bluepylons/Open-Switch-Curve-Meter/Pics/Gen-2-front-no-keycap.JPG

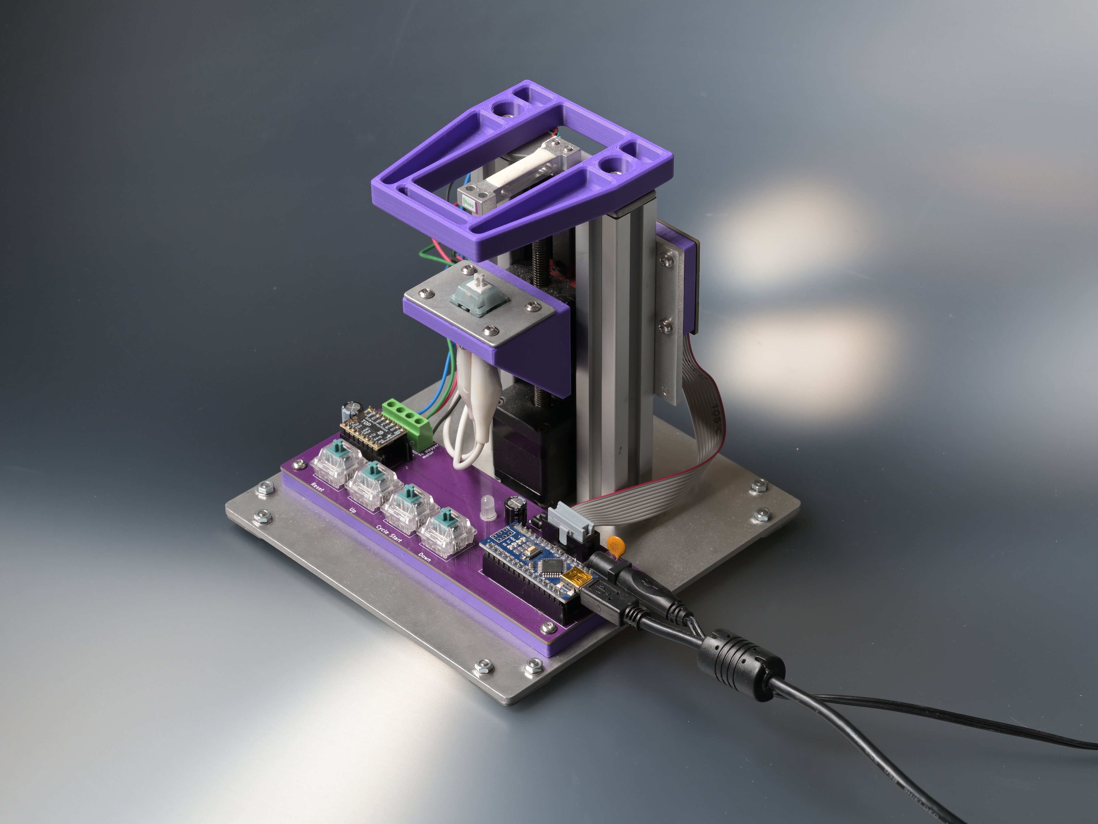
Pics/Gen-2-front-no-keycap.JPG
