bluepylons/Open-Switch-Curve-Meter/Pics/Gen-2.JPG

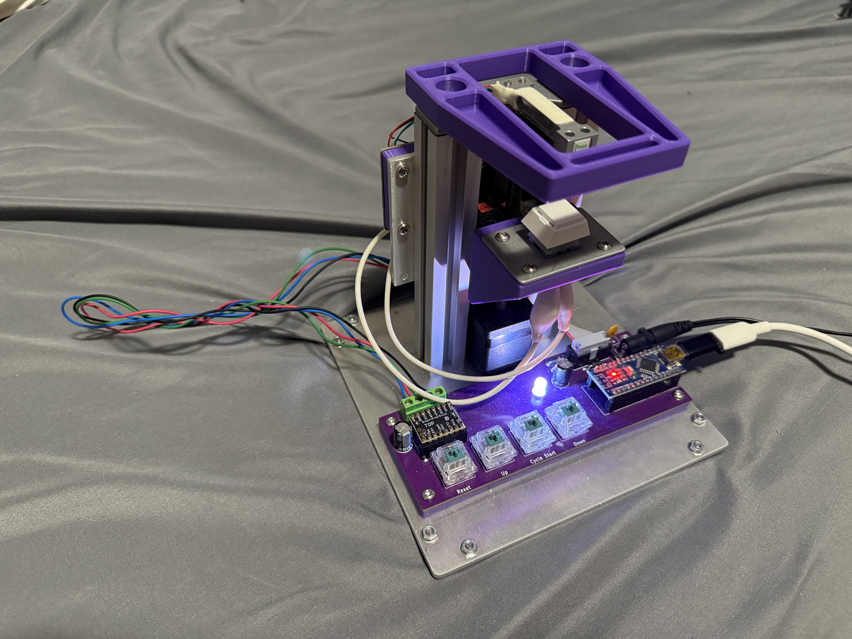
Pics/Gen-2.JPG
