bluepylons/Open-Switch-Curve-Meter/Pics/IMG_0680.JPG

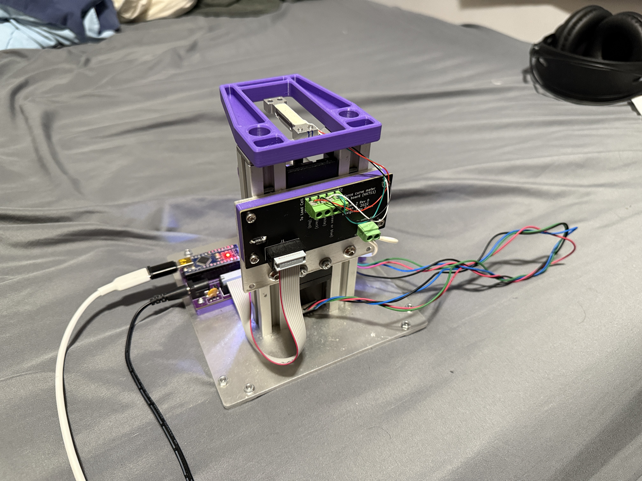
Pics/IMG_0680.JPG
