bluepylons/Open-Switch-Curve-Meter/Pics/Prototype-1-vertical.jpg

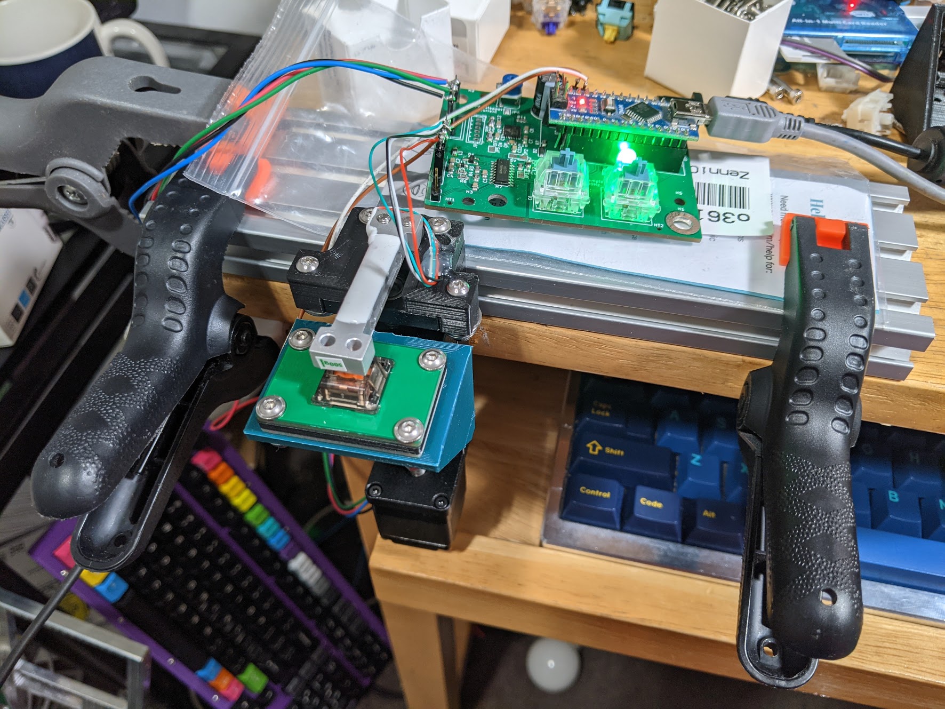
Pics/Prototype-1-vertical.jpg
