bluepylons/Open-Switch-Curve-Meter/Pics/Prototype-1.jpg

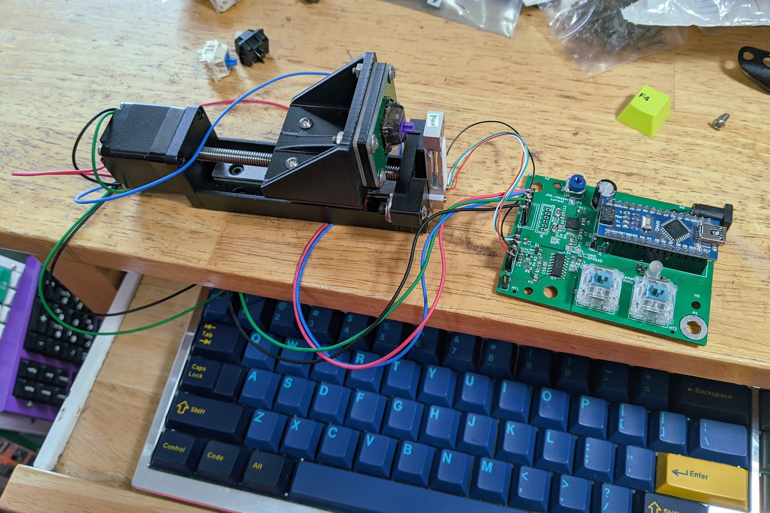
Pics/Prototype-1.jpg
