bluepylons/Open-Switch-Curve-Meter/Gen 2 Design/Mechanical files/Laser cut/Load-cell-mounting-plate.stp

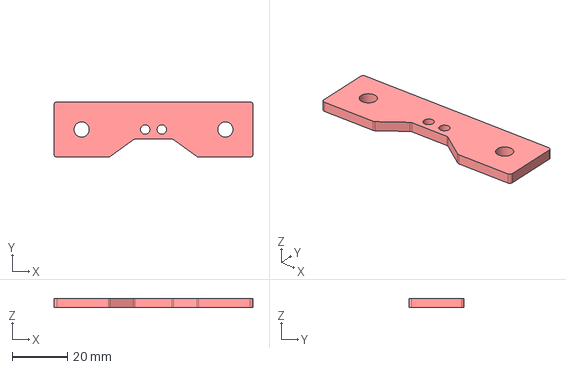
[picture p144: CAD file, 2026-01-06]
Gen 2 Design/Mechanical files/Laser cut/Load-cell-mounting-plate.stp
72.0 x 20.0 x 3.17 mm
