bluepylons/Open-Switch-Curve-Meter/CAD (Atom3D)/STLs/Switch-mounting-bracket.stl

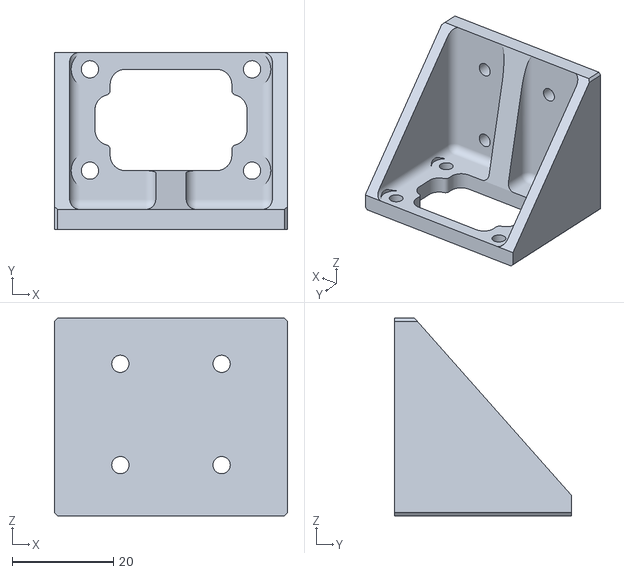
[picture p145: CAD file, 2021-06-18]
CAD (Atom3D)/STLs/Switch-mounting-bracket.stl
46.0 x 35.0 x 39.0
