bluepylons/Open-Switch-Curve-Meter/Gen 2 Design/Mechanical files/Laser cut/Baseplate-stand.stp

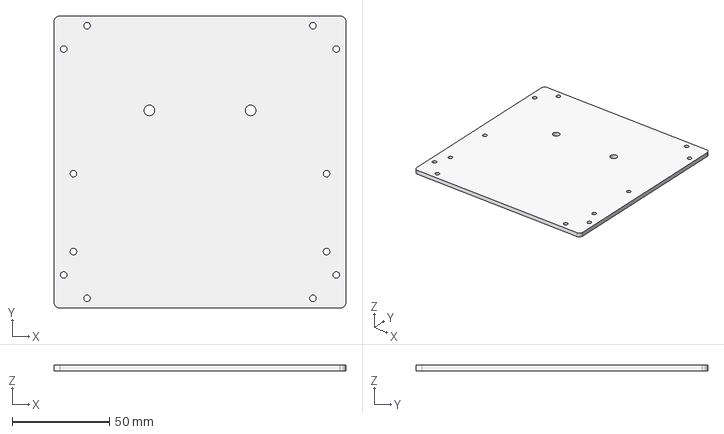
[picture p146: CAD file, 2026-01-06]
Gen 2 Design/Mechanical files/Laser cut/Baseplate-stand.stp
150.0 x 150.0 x 3.17 mm
