bluepylons/Open-Switch-Curve-Meter/Gen 2 Design/Mechanical files/Atom3D CAD files/M3-hex-nut-DIN-934.step

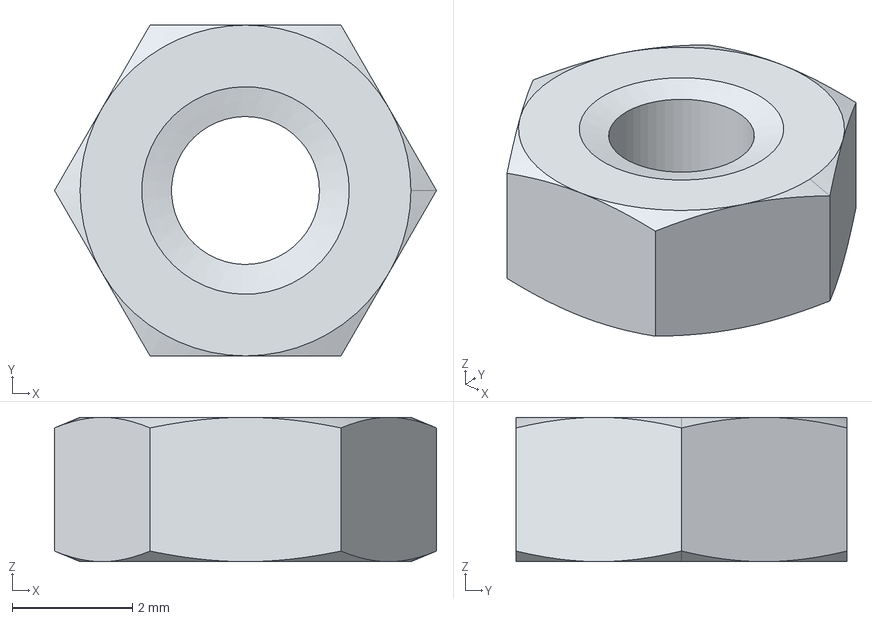
[picture p147: CAD file, 2026-01-05]
Gen 2 Design/Mechanical files/Atom3D CAD files/M3-hex-nut-DIN-934.step
6.35 x 5.50 x 2.40 mm
