bluepylons/Open-Switch-Curve-Meter/Force curves/Okay-I'm-Just-Going-to-Calibrate-Every-Day-Now/Feker-Smoky-Tactile-Stem-In-T1-Housing.ods

Raw data |  |  |  | Corrected Downstroke |  | Corrected Upstroke
X (microns) | Force (gf) | Actuated? | Tared | X (mm) | Force (gf) | X (mm) | Force (gf)
0 | -0.03 | 0 |  | 0 | 0.51 | 2.785 | 91.39
5 | -0.02 | 0 |  | 0.005 | 3.07 | 2.78 | 75.15
10 | -0.02 | 0 |  | 0.01 | 16.92 | 2.775 | 67.36
15 | -0.06 | 0 |  | 0.015 | 23.72 | 2.77 | 54.02
20 | -0.02 | 0 |  | 0.02 | 25.77 | 2.765 | 52.09
25 | -0.02 | 0 |  | 0.025 | 25.64 | 2.76 | 51.23
30 | -0.02 | 0 |  | 0.03 | 25.82 | 2.755 | 50.56
35 | -0.03 | 0 |  | 0.035 | 26.11 | 2.75 | 50.32
40 | -0.01 | 0 |  | 0.04 | 28.4 | 2.745 | 49.74
45 | -0.01 | 0 |  | 0.045 | 30.32 | 2.74 | 49.52
50 | 0 | 0 |  | 0.05 | 32.86 | 2.735 | 48.82
55 | 0 | 0 |  | 0.055 | 33.33 | 2.73 | 48.6
60 | -0.02 | 0 |  | 0.06 | 33.56 | 2.725 | 48.03
65 | -0.01 | 0 |  | 0.065 | 33.83 | 2.72 | 47.85
70 | 0 | 0 |  | 0.07 | 34.03 | 2.715 | 47.09
75 | -0.01 | 0 |  | 0.075 | 34.58 | 2.71 | 46.87
80 | 0 | 0 |  | 0.08 | 34.84 | 2.705 | 46.27
85 | -0.02 | 0 |  | 0.085 | 35.52 | 2.7 | 46.1
90 | 0 | 0 |  | 0.09 | 35.88 | 2.695 | 45.35
95 | -0.01 | 0 |  | 0.095 | 36.65 | 2.69 | 45.08
100 | 0.01 | 0 |  | 0.1 | 36.83 | 2.685 | 44.39
105 | 0.03 | 0 |  | 0.105 | 37.09 | 2.68 | 44.19
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
