bluepylons/Open-Switch-Curve-Meter/Force curves/Okay-I'm-Just-Going-to-Calibrate-Every-Day-Now/NK-Blueberry-stem-in-Tecsee-Lychee.ods

Raw data |  |  |  | Corrected Downstroke |  | Corrected Upstroke
X (microns) | Force (gf) | Actuated? | Tared | X (mm) | Force (gf) | X (mm) | Force (gf)
0 | -0.05 | 0 | 0 | 0 | 0.42 | 3.72 | 67.65
5 | -0.04 | 0 | 0.01 | 0.005 | 9.39 | 3.715 | 67.37
10 | -0.03 | 0 | 0.02 | 0.01 | 16.71 | 3.71 | 67.28
15 | -0.05 | 0 | 0 | 0.015 | 31.33 | 3.705 | 67.06
20 | -0.02 | 0 | 0.03 | 0.02 | 38.25 | 3.7 | 66.91
25 | -0.06 | 0 | -0.01 | 0.025 | 45.42 | 3.695 | 66.81
30 | -0.06 | 0 | -0.01 | 0.03 | 47.04 | 3.69 | 66.65
35 | -0.03 | 0 | 0.02 | 0.035 | 49.03 | 3.685 | 66.52
40 | -0.04 | 0 | 0.01 | 0.04 | 49.46 | 3.68 | 66.21
45 | -0.05 | 0 | 0 | 0.045 | 49.41 | 3.675 | 66.19
50 | -0.04 | 0 | 0.01 | 0.05 | 49.43 | 3.67 | 65.96
55 | -0.05 | 0 | 0 | 0.055 | 49.05 | 3.665 | 65.89
60 | -0.03 | 0 | 0.02 | 0.06 | 48.96 | 3.66 | 65.76
65 | -0.03 | 0 | 0.02 | 0.065 | 48.92 | 3.655 | 65.71
70 | -0.03 | 0 | 0.02 | 0.07 | 49.04 | 3.65 | 65.51
75 | -0.05 | 0 | 0 | 0.075 | 49.07 | 3.645 | 65.44
80 | -0.07 | 0 | -0.02 | 0.08 | 48.9 | 3.64 | 65.32
85 | -0.06 | 0 | -0.01 | 0.085 | 48.72 | 3.635 | 65.23
90 | 0 | 0 | 0.05 | 0.09 | 48.79 | 3.63 | 65
95 | -0.01 | 0 | 0.04 | 0.095 | 48.72 | 3.625 | 64.91
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
