bluepylons/Open-Switch-Curve-Meter/Force curves/Okay-I'm-Just-Going-to-Calibrate-Every-Day-Now/Durock-Shrimp.ods

Raw data |  |  |  | Corrected Downstroke |  | Corrected Upstroke
X (microns) | Force (gf) | Actuated? | Tared | X (mm) | Force (gf) | X (mm) | Force (gf)
0 | -0.02 | 0 | 0 | 0 | 3.27 | 3.37 | 108.52
5 | -0.03 | 0 | -0.01 | 0.005 | 7.87 | 3.365 | 104.4
10 | -0.01 | 0 | 0.01 | 0.01 | 17.7 | 3.36 | 97.14
15 | -0.03 | 0 | -0.01 | 0.015 | 22.87 | 3.355 | 93.87
20 | -0.04 | 0 | -0.02 | 0.02 | 29.94 | 3.35 | 88.1
25 | -0.02 | 0 | 0 | 0.025 | 31.75 | 3.345 | 85.55
30 | -0.03 | 0 | -0.01 | 0.03 | 35.33 | 3.34 | 81.15
35 | -0.03 | 0 | -0.01 | 0.035 | 37.24 | 3.335 | 77.59
40 | -0.02 | 0 | 0 | 0.04 | 41.13 | 3.33 | 75.82
45 | -0.01 | 0 | 0.01 | 0.045 | 44.83 | 3.325 | 72.72
50 | 0 | 0 | 0.02 | 0.05 | 46.64 | 3.32 | 71.4
55 | 0.01 | 0 | 0.03 | 0.055 | 49.84 | 3.315 | 69.27
60 | -0.04 | 0 | -0.02 | 0.06 | 51.35 | 3.31 | 68.26
65 | -0.02 | 0 | 0 | 0.065 | 53.95 | 3.305 | 66.72
70 | -0.01 | 0 | 0.01 | 0.07 | 55.09 | 3.3 | 65.96
75 | -0.02 | 0 | 0 | 0.075 | 56.88 | 3.295 | 64.92
80 | -0.05 | 0 | -0.03 | 0.08 | 57.79 | 3.29 | 64.85
85 | 0.02 | 0 | 0.04 | 0.085 | 59.82 | 3.285 | 64.71
90 | 0.02 | 0 | 0.04 | 0.09 | 60.61 | 3.28 | 64.5
95 | -0.03 | 0 | -0.01 | 0.095 | 61.62 | 3.275 | 64.06
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
