bluepylons/Open-Switch-Curve-Meter/Force curves/Okay-I'm-Just-Going-to-Calibrate-Every-Day-Now/Gateron-Silver-Blizzard.ods

Raw data |  |  |  | Corrected Downstroke |  | Corrected Upstroke
X (microns) | Force (gf) | Actuated? | Tared | X (mm) | Force (gf) | X (mm) | Force (gf)
0 | 0.05 | 0 | 0 | 0 | 7 | 3.405 | 116.66
5 | 0.03 | 0 | -0.02 | 0.005 | 20.95 | 3.4 | 106.08
10 | 0.07 | 0 | 0.02 | 0.01 | 28.46 | 3.395 | 95.47
15 | 0.07 | 0 | 0.02 | 0.015 | 34.38 | 3.39 | 90.1
20 | 0.07 | 0 | 0.02 | 0.02 | 36.03 | 3.385 | 80.31
25 | 0.06 | 0 | 0.01 | 0.025 | 39.83 | 3.38 | 75.6
30 | 0.06 | 0 | 0.01 | 0.03 | 41.95 | 3.375 | 67.47
35 | 0.1 | 0 | 0.05 | 0.035 | 43.49 | 3.37 | 63.79
40 | 0.09 | 0 | 0.04 | 0.04 | 43.68 | 3.365 | 60.44
45 | 0.06 | 0 | 0.01 | 0.045 | 43.7 | 3.36 | 60.06
50 | 0.06 | 0 | 0.01 | 0.05 | 43.78 | 3.355 | 59.96
55 | 0.07 | 0 | 0.02 | 0.055 | 43.83 | 3.35 | 59.39
60 | 0.08 | 0 | 0.03 | 0.06 | 43.97 | 3.345 | 59
65 | 0.08 | 0 | 0.03 | 0.065 | 44.25 | 3.34 | 58.92
70 | 0.05 | 0 | 0 | 0.07 | 44.45 | 3.335 | 58.85
75 | 0.07 | 0 | 0.02 | 0.075 | 44.85 | 3.33 | 58.87
80 | 0.07 | 0 | 0.02 | 0.08 | 45.16 | 3.325 | 58.83
85 | 0.05 | 0 | 0 | 0.085 | 45.56 | 3.31999999999999 | 58.83
90 | 0.06 | 0 | 0.01 | 0.09 | 45.76 | 3.31499999999999 | 58.77
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
