bluepylons/Open-Switch-Curve-Meter/Force curves/Okay-I'm-Just-Going-to-Calibrate-Every-Day-Now/Gateron-Slate.ods

Raw data |  |  |  | Corrected Downstroke |  | Corrected Upstroke
X (microns) | Force (gf) | Actuated? | Tared | X (mm) | Force (gf) | X (mm) | Force (gf)
0 | 0.03 | 0 |  | 0 | 0.48 | 3.29 | 121
5 | 0.03 | 0 |  | 0.005 | 3.63 | 3.285 | 111.89
10 | 0.03 | 0 |  | 0.01 | 8.76 | 3.28 | 94.68
15 | 0.03 | 0 |  | 0.015 | 10.79 | 3.275 | 85.71
20 | 0.02 | 0 |  | 0.02 | 13.8 | 3.27 | 69.55
25 | 0 | 0 |  | 0.025 | 15.12 | 3.265 | 62.01
30 | 0 | 0 |  | 0.03 | 16.96 | 3.26 | 52.27
35 | 0 | 0 |  | 0.035 | 17.58 | 3.255 | 51.31
40 | -0.01 | 0 |  | 0.04 | 17.63 | 3.25 | 51.12
45 | 0.01 | 0 |  | 0.045 | 17.48 | 3.245 | 51.04
50 | -0.02 | 0 |  | 0.05 | 17.34 | 3.24 | 51.08
55 | -0.02 | 0 |  | 0.055 | 17.4 | 3.235 | 51.02
60 | -0.01 | 0 |  | 0.06 | 17.5 | 3.23 | 51.11
65 | -0.02 | 0 |  | 0.065 | 17.58 | 3.225 | 51.02
70 | -0.04 | 0 |  | 0.07 | 17.74 | 3.22 | 50.96
75 | -0.02 | 0 |  | 0.075 | 23.82 | 3.215 | 50.72
80 | -0.05 | 0 |  | 0.08 | 28.02 | 3.21 | 50.77
85 | -0.04 | 0 |  | 0.085 | 30.29 | 3.205 | 50.66
90 | -0.06 | 0 |  | 0.09 | 30.11 | 3.2 | 50.66
95 | -0.03 | 0 |  | 0.095 | 30.1 | 3.195 | 50.61
100 | -0.06 | 0 |  | 0.1 | 30.07 | 3.19 | 50.59
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
