bluepylons/Open-Switch-Curve-Meter/Force curves/Okay-I'm-Just-Going-to-Calibrate-Every-Day-Now/KTT-Kang-White.ods

Raw data |  |  |  | Corrected Downstroke |  | Corrected Upstroke
X (microns) | Force (gf) | Actuated? | Tared | X (mm) | Force (gf) | X (mm) | Force (gf)
0 | 0.2 | 0 | -0.01 | 0 | 0.37 | 3.615 | 123.38
5 | 0.18 | 0 | -0.03 | 0.005 | 0.93 | 3.61 | 117.54
10 | 0.19 | 0 | -0.02 | 0.01 | 6.01 | 3.605 | 104.13
15 | 0.17 | 0 | -0.04 | 0.015 | 10.67 | 3.6 | 97.31
20 | 0.18 | 0 | -0.03 | 0.02 | 19.53 | 3.595 | 83.08
25 | 0.17 | 0 | -0.04 | 0.025 | 22.4 | 3.59 | 76.4
30 | 0.15 | 0 | -0.06 | 0.03 | 26.92 | 3.585 | 63.38
35 | 0.15 | 0 | -0.06 | 0.035 | 27.87 | 3.58 | 58.81
40 | 0.16 | 0 | -0.05 | 0.04 | 28.86 | 3.575 | 55.71
45 | 0.17 | 0 | -0.04 | 0.045 | 28.75 | 3.57 | 55.43
50 | 0.2 | 0 | -0.01 | 0.05 | 28.42 | 3.565 | 55.35
55 | 0.21 | 0 | 0 | 0.055 | 28.39 | 3.56 | 55.22
60 | 0.18 | 0 | -0.03 | 0.06 | 28.32 | 3.555 | 55.17
65 | 0.2 | 0 | -0.01 | 0.065 | 28.28 | 3.55 | 55.06
70 | 0.21 | 0 | 0 | 0.07 | 28.13 | 3.545 | 54.98
75 | 0.2 | 0 | -0.01 | 0.075 | 28.07 | 3.54 | 54.87
80 | 0.2 | 0 | -0.01 | 0.08 | 28.02 | 3.535 | 54.81
85 | 0.23 | 0 | 0.02 | 0.085 | 27.96 | 3.52999999999999 | 54.68
90 | 0.17 | 0 | -0.04 | 0.09 | 28 | 3.52499999999999 | 54.62
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
