bluepylons/Open-Switch-Curve-Meter/Force curves/Okay-I'm-Just-Going-to-Calibrate-Every-Day-Now/Tecsee-Lychee.ods

Raw data |  |  |  | Corrected Downstroke |  | Corrected Upstroke
X (microns) | Force (gf) | Actuated? | Tared | X (mm) | Force (gf) | X (mm) | Force (gf)
0 | 0.16 | 0 | 0 | 0 | 0.09 | 3.88 | 80.56
5 | 0.16 | 0 | 0 | 0.005 | 0.5 | 3.875 | 75.22
10 | 0.16 | 0 | 0 | 0.01 | 10.38 | 3.87 | 72.97
15 | 0.16 | 0 | 0 | 0.015 | 16.93 | 3.865 | 70.99
20 | 0.18 | 0 | 0.02 | 0.02 | 30.21 | 3.86 | 70.44
25 | 0.19 | 0 | 0.03 | 0.025 | 36.76 | 3.855 | 69.81
30 | 0.18 | 0 | 0.02 | 0.03 | 47.93 | 3.85 | 69.46
35 | 0.18 | 0 | 0.02 | 0.035 | 52.2 | 3.845 | 68.75
40 | 0.18 | 0 | 0.02 | 0.04 | 55.65 | 3.84 | 68.3
45 | 0.18 | 0 | 0.02 | 0.045 | 55.68 | 3.835 | 67.7
50 | 0.19 | 0 | 0.03 | 0.05 | 55.62 | 3.83 | 67.52
55 | 0.17 | 0 | 0.01 | 0.055 | 55.86 | 3.825 | 67.38
60 | 0.17 | 0 | 0.01 | 0.06 | 56.45 | 3.82 | 67.32
65 | 0.19 | 0 | 0.03 | 0.065 | 56.6 | 3.815 | 67.25
70 | 0.17 | 0 | 0.01 | 0.07 | 56.8 | 3.81 | 67.18
75 | 0.18 | 0 | 0.02 | 0.075 | 56.74 | 3.805 | 67.11
80 | 0.21 | 0 | 0.05 | 0.08 | 56.82 | 3.8 | 67.1
85 | 0.19 | 0 | 0.03 | 0.085 | 56.94 | 3.795 | 67.03
90 | 0.17 | 0 | 0.01 | 0.09 | 57.11 | 3.79 | 66.96
95 | 0.21 | 0 | 0.05 | 0.095 | 57.2 | 3.785 | 66.93
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
