bluepylons/Open-Switch-Curve-Meter/Force curves/Okay-I'm-Just-Going-to-Calibrate-Every-Day-Now/Tecsee-Ruby-V1.ods

Raw data |  |  |  | Corrected Downstroke |  | Corrected Upstroke
X (microns) | Force (gf) | Actuated? | Tared | X (mm) | Force (gf) | X (mm) | Force (gf)
0 | 0 | 0 |  | 0 | 0.15 | 3.415 | 71.68
5 | -0.01 | 0 |  | 0.005 | 7.84 | 3.41 | 71.55
10 | 0 | 0 |  | 0.01 | 15.3 | 3.405 | 71.46
15 | -0.02 | 0 |  | 0.015 | 26.64 | 3.4 | 71.39
20 | 0.01 | 0 |  | 0.02 | 28.04 | 3.395 | 71.31
25 | -0.01 | 0 |  | 0.025 | 29.13 | 3.39 | 71.19
30 | -0.01 | 0 |  | 0.03 | 29.69 | 3.385 | 71.08
35 | -0.02 | 0 |  | 0.035 | 30.95 | 3.38 | 71.01
40 | -0.04 | 0 |  | 0.04 | 31.38 | 3.375 | 70.97
45 | -0.05 | 0 |  | 0.045 | 32.06 | 3.37 | 70.89
50 | -0.02 | 0 |  | 0.05 | 32.1 | 3.365 | 70.73
55 | -0.04 | 0 |  | 0.055 | 31.86 | 3.36 | 70.72
60 | -0.04 | 0 |  | 0.06 | 31.78 | 3.355 | 70.66
65 | -0.03 | 0 |  | 0.065 | 31.7 | 3.35 | 70.62
70 | -0.02 | 0 |  | 0.07 | 31.69 | 3.345 | 70.49
75 | -0.07 | 0 |  | 0.075 | 31.49 | 3.34 | 70.42
80 | -0.05 | 0 |  | 0.08 | 31.5 | 3.335 | 70.38
85 | -0.06 | 0 |  | 0.085 | 31.43 | 3.33 | 70.33
90 | -0.05 | 0 |  | 0.09 | 31.17 | 3.325 | 70.23
95 | -0.08 | 0 |  | 0.095 | 31.07 | 3.32 | 70.18
100 | -0.07 | 0 |  | 0.1 | 31.08 | 3.315 | 70.09
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
