bluepylons/Open-Switch-Curve-Meter/Force curves/Okay-I'm-Just-Going-to-Calibrate-Every-Day-Now/Tecsee-Sapphire-V1.ods

Raw data |  |  |  | Corrected Downstroke |  | Corrected Upstroke
X (microns) | Force (gf) | Actuated? | Tared | X (mm) | Force (gf) | X (mm) | Force (gf)
0 | 0.09 | 0 | 0 | 0 | 0.23 | 3.255 | 92.88
5 | 0.09 | 0 | 0 | 0.005 | 8.58 | 3.25 | 86.68
10 | 0.09 | 0 | 0 | 0.01 | 15.42 | 3.245 | 74.55
15 | 0.07 | 0 | -0.02 | 0.015 | 27.36 | 3.24 | 67.64
20 | 0.02 | 0 | -0.07 | 0.02 | 33.07 | 3.235 | 67.29
25 | 0.06 | 0 | -0.03 | 0.025 | 40.42 | 3.23 | 67.05
30 | 0.04 | 0 | -0.05 | 0.03 | 41.7 | 3.225 | 66.92
35 | 0.06 | 0 | -0.03 | 0.035 | 42.23 | 3.22 | 66.75
40 | 0.04 | 0 | -0.05 | 0.04 | 42.4 | 3.215 | 66.79
45 | 0.06 | 0 | -0.03 | 0.045 | 42.26 | 3.21 | 66.64
50 | 0.03 | 0 | -0.06 | 0.05 | 42.3 | 3.205 | 66.54
55 | 0.05 | 0 | -0.04 | 0.055 | 42.14 | 3.2 | 66.49
60 | 0.05 | 0 | -0.04 | 0.06 | 41.88 | 3.195 | 66.4
65 | 0.07 | 0 | -0.02 | 0.065 | 41.19 | 3.19 | 66.34
70 | 0.04 | 0 | -0.05 | 0.07 | 40.39 | 3.185 | 66.2
75 | 0.07 | 0 | -0.02 | 0.075 | 40.14 | 3.18 | 66.24
80 | 0.06 | 0 | -0.03 | 0.08 | 40.63 | 3.175 | 66.14
85 | 0.07 | 0 | -0.02 | 0.085 | 40.9 | 3.17 | 66.01
90 | 0.07 | 0 | -0.02 | 0.09 | 41.75 | 3.165 | 66.06
95 | 0.09 | 0 | 0 | 0.095 | 42.38 | 3.16 | 65.96
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
