bluepylons/Open-Switch-Curve-Meter/Force curves/Okay-I'm-Just-Going-to-Calibrate-Every-Day-Now/TTC-Golden-Blue.ods

Raw data |  |  |  | Corrected Downstroke |  | Corrected Upstroke
X (microns) | Force (gf) | Actuated? | Tared | X (mm) | Force (gf) | X (mm) | Force (gf)
0 | 0.02 | 0 |  | 0 | 0.22 | 3.535 | 109.77
5 | 0.03 | 0 |  | 0.005 | 0.94 | 3.53 | 108.25
10 | 0.04 | 0 |  | 0.01 | 2.49 | 3.525 | 105.28
15 | -0.01 | 0 |  | 0.015 | 3.18 | 3.52 | 103.77
20 | -0.01 | 0 |  | 0.02 | 4.56 | 3.515 | 100.98
25 | 0.01 | 0 |  | 0.025 | 5.87 | 3.51 | 99.6
30 | 0.22 | 0 |  | 0.03 | 6.56 | 3.505 | 97.11
35 | 0.94 | 0 |  | 0.035 | 7.9 | 3.5 | 95.85
40 | 2.49 | 0 |  | 0.04 | 8.48 | 3.495 | 93.5
45 | 3.18 | 0 |  | 0.045 | 8.53 | 3.49 | 92.38
50 | 4.56 | 0 |  | 0.05 | 8.28 | 3.485 | 90.15
55 | 5.87 | 0 |  | 0.055 | 8.57 | 3.48 | 89.03
60 | 6.56 | 0 |  | 0.06 | 11.39 | 3.475 | 86.8
65 | 7.9 | 0 |  | 0.065 | 16.45 | 3.47 | 85.64
70 | 8.48 | 0 |  | 0.07 | 16.66 | 3.465 | 83.03
75 | 8.53 | 0 |  | 0.075 | 16.46 | 3.46 | 80.11
80 | 8.28 | 0 |  | 0.08 | 16.36 | 3.455 | 78.58
85 | 8.57 | 0 |  | 0.085 | 16.14 | 3.45 | 75.7
90 | 11.39 | 0 |  | 0.09 | 16 | 3.445 | 74.25
95 | 16.45 | 0 |  | 0.095 | 15.83 | 3.44 | 71.49
100 | 16.66 | 0 |  | 0.1 | 16.03 | 3.435 | 70.08
105 | 16.46 | 0 |  | 0.105 | 16.57 | 3.43 | 67.58
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
