bluepylons/Open-Switch-Curve-Meter/Force curves/Okay-I'm-Just-Going-to-Calibrate-Every-Day-Now/TTC-Watermelon-Milkshake.ods

Raw data |  |  |  | Corrected Downstroke |  | Corrected Upstroke
X (microns) | Force (gf) | Actuated? | Tared | X (mm) | Force (gf) | X (mm) | Force (gf)
0 | -0.14 | 0 | -0.04 | 0 | 0.05 | 3.945 | 122.19
5 | -0.1 | 0 | 0 | 0.005 | 5.1 | 3.94 | 114.53
10 | -0.08 | 0 | 0.02 | 0.01 | 11.77 | 3.935 | 99.52
15 | -0.08 | 0 | 0.02 | 0.015 | 23.43 | 3.93 | 92.63
20 | -0.08 | 0 | 0.02 | 0.02 | 28.38 | 3.925 | 81.51
25 | -0.09 | 0 | 0.01 | 0.025 | 34.61 | 3.92 | 79.24
30 | -0.1 | 0 | 0 | 0.03 | 35.58 | 3.915 | 75.75
35 | -0.09 | 0 | 0.01 | 0.035 | 36.18 | 3.91 | 70.5
40 | -0.09 | 0 | 0.01 | 0.04 | 36.2 | 3.905 | 67.71
45 | -0.1 | 0 | 0 | 0.045 | 36.03 | 3.9 | 63.37
50 | -0.12 | 0 | -0.02 | 0.05 | 36.03 | 3.895 | 62.75
55 | -0.05 | 0 | 0.05 | 0.055 | 36.09 | 3.89 | 62.47
60 | 5 | 0 | 5.1 | 0.06 | 36.12 | 3.885 | 62.5
65 | 11.67 | 0 | 11.77 | 0.065 | 36.19 | 3.88 | 62.4
70 | 23.33 | 0 | 23.43 | 0.07 | 36.3 | 3.875 | 62.4
75 | 28.28 | 0 | 28.38 | 0.075 | 36.29 | 3.87 | 62.28
80 | 34.51 | 0 | 34.61 | 0.08 | 36.26 | 3.865 | 62.25
85 | 35.48 | 0 | 35.58 | 0.085 | 36.27 | 3.86 | 62.14
90 | 36.08 | 0 | 36.18 | 0.09 | 36.29 | 3.855 | 62.14
95 | 36.1 | 0 | 36.2 | 0.095 | 36.26 | 3.85 | 62.15
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
