bluepylons/Open-Switch-Curve-Meter/Force curves/Okay-I'm-Just-Going-to-Calibrate-Every-Day-Now/Durock-T1-stem-in-Harimau-housing-T1-comparison.ods

Raw data |  |  |  | Corrected Downstroke |  | Corrected Upstroke |  | Stock T1 Corrected Downstroke |  | Corrected Upstroke
X (microns) | Force (gf) | Actuated? | Tared | X (mm) | Force (gf) | X (mm) | Force (gf) | X (mm) | Force (gf) | X (mm) | Force (gf)
0 | -0.13 | 0 | -0.02 | 0 | 0.72 | 3.895 | 74.53 | 0 | 8.18 | 3.89 | 89.67
5 | -0.12 | 0 | -0.01 | 0.005 | 3.64 | 3.89 | 68.44 | 0.005 | 21.53 | 3.885 | 77.07
10 | -0.1 | 0 | 0.01 | 0.01 | 16.98 | 3.885 | 63.83 | 0.01 | 28.17 | 3.88 | 71.03
15 | -0.1 | 0 | 0.01 | 0.015 | 24.13 | 3.88 | 63.89 | 0.015 | 38.72 | 3.875 | 63.51
20 | -0.12 | 0 | -0.01 | 0.02 | 35.01 | 3.875 | 63.57 | 0.02 | 41.55 | 3.87 | 63.14
25 | -0.09 | 0 | 0.02 | 0.025 | 36.32 | 3.87 | 63.69 | 0.025 | 42.72 | 3.865 | 63.06
30 | -0.09 | 0 | 0.02 | 0.03 | 36.93 | 3.865 | 63.37 | 0.03 | 43.15 | 3.86 | 63.4
35 | -0.1 | 0 | 0.01 | 0.035 | 37.18 | 3.86 | 63.51 | 0.035 | 42.88 | 3.855 | 63.27
40 | -0.11 | 0 | 0 | 0.04 | 38.1 | 3.855 | 63.47 | 0.04 | 43.29 | 3.85 | 63.56
45 | -0.11 | 0 | 0 | 0.045 | 38.62 | 3.85 | 63.58 | 0.045 | 43.33 | 3.845 | 63.5
50 | -0.1 | 0 | 0.01 | 0.05 | 39.69 | 3.845 | 63.42 | 0.05 | 43.42 | 3.84 | 63.98
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
