bluepylons/Open-Switch-Curve-Meter/Force curves/Okay-I'm-Just-Going-to-Calibrate-Every-Day-Now/JWK-Twilight-stock.ods

Raw data |  |  |  | Corrected Downstroke |  | Corrected Upstroke
X (microns) | Force (gf) | Actuated? | Tared | X (mm) | Force (gf) | X (mm) | Force (gf)
0 | -0.03 | 0
5 | 0 | 0
10 | -0.01 | 0
15 | 0.01 | 0
20 | -0.01 | 0
25 | 0 | 0
30 | 0 | 0
35 | 0 | 0
40 | -0.02 | 0
45 | 0.02 | 0
50 | 0.03 | 0
55 | 0.02 | 0
60 | 0.01 | 0
65 | 0.48 | 0
70 | 3.01 | 0
75 | 16.35 | 0
80 | 24.31 | 0
85 | 33.17 | 0
90 | 34.72 | 0
95 | 36.68 | 0
100 | 37.53 | 0
105 | 38.6 | 0
110 | 38.84 | 0
115 | 39.4 | 0
120 | 39.22 | 0
125 | 38.9 | 0
130 | 38.47 | 0
135 | 38.36 | 0
140 | 38.22 | 0
145 | 38.16 | 0
150 | 37.97 | 0
155 | 37.89 | 0
160 | 37.67 | 0
165 | 37.62 | 0
170 | 37.62 | 0
175 | 37.71 | 0
180 | 37.73 | 0
185 | 37.85 | 0
190 | 38.05 | 0
195 | 38.33 | 0
200 | 38.45 | 0
205 | 38.67 | 0
210 | 38.72 | 0
215 | 38.67 | 0
220 | 38.64 | 0
225 | 38.59 | 0
230 | 38.57 | 0
235 | 38.56 | 0
240 | 38.56 | 0
245 | 38.4 | 0
250 | 38.3 | 0
255 | 38.18 | 0
260 | 38.06 | 0
265 | 38 | 0
270 | 37.91 | 0
275 | 37.76 | 0 |  |  |  |  |  | Actuation
280 | 37.67 | 0 |  |  |  |  |  |  | 41
285 | 37.81 | 0 |  |  |  |  |  |  | 51
290 | 37.79 | 0
295 | 37.78 | 0 |  |  |  |  |  | Release
300 | 37.69 | 0 |  |  |  |  |  |  | 15
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
