bluepylons/Open-Switch-Curve-Meter/Force curves/Okay-I'm-Just-Going-to-Calibrate-Every-Day-Now/Koala-stem-in-Moyu-Black-housing.ods

Raw data |  |  |  | Corrected Downstroke |  | Corrected Upstroke
X (microns) | Force (gf) | Actuated? | Tared | X (mm) | Force (gf) | X (mm) | Force (gf)
0 | -0.14 | 0
5 | -0.12 | 0
10 | -0.12 | 0
15 | -0.1 | 0
20 | -0.16 | 0
25 | -0.13 | 0
30 | -0.14 | 0
35 | -0.14 | 0
40 | -0.14 | 0
45 | -0.14 | 0
50 | -0.14 | 0
55 | -0.13 | 0
60 | -0.14 | 0
65 | -0.16 | 0
70 | -0.16 | 0
75 | -0.17 | 0
80 | -0.15 | 0
85 | -0.15 | 0
90 | -0.12 | 0
95 | -0.16 | 0
100 | -0.14 | 0
105 | -0.11 | 0
110 | -0.13 | 0
115 | -0.14 | 0
120 | -0.16 | 0
125 | -0.12 | 0
130 | -0.14 | 0
135 | -0.13 | 0
140 | -0.13 | 0
145 | -0.16 | 0
150 | -0.16 | 0
155 | -0.12 | 0
160 | -0.16 | 0
165 | -0.16 | 0
170 | -0.11 | 0
175 | -0.11 | 0
180 | -0.14 | 0
185 | -0.13 | 0
190 | -0.13 | 0
195 | -0.14 | 0
200 | -0.13 | 0
205 | -0.14 | 0
210 | -0.13 | 0
215 | -0.11 | 0
220 | -0.11 | 0
225 | -0.13 | 0
230 | -0.1 | 0
235 | -0.12 | 0
240 | -0.12 | 0
245 | -0.14 | 0
250 | -0.11 | 0
255 | -0.16 | 0
260 | -0.16 | 0
265 | -0.15 | 0
270 | -0.14 | 0
275 | -0.13 | 0 |  |  |  |  |  | Actuation
280 | -0.13 | 0 |  |  |  |  |  |  | 41
285 | -0.13 | 0 |  |  |  |  |  |  | 51
290 | -0.14 | 0
295 | -0.14 | 0 |  |  |  |  |  | Release
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
