bluepylons/Open-Switch-Curve-Meter/Force curves/Okay-I'm-Just-Going-to-Calibrate-Every-Day-Now/Rebult-Harimau-Stem-In-T1.ods

Raw data |  |  |  | Corrected Downstroke |  | Corrected Upstroke
X (microns) | Force (gf) | Actuated? | Tared | X (mm) | Force (gf) | X (mm) | Force (gf)
0 | 0.13 | 0 | 0 | 0 | 1.28 | 3.005 | 100.45
5 | 0.14 | 0 | 0.01 | 0.005 | 6.72 | 3 | 85.34
10 | 0.15 | 0 | 0.02 | 0.01 | 20.2 | 2.995 | 78.09
15 | 0.14 | 0 | 0.01 | 0.015 | 23.13 | 2.99 | 63.47
20 | 0.15 | 0 | 0.02 | 0.02 | 24.32 | 2.985 | 58.72
25 | 0.13 | 0 | 0 | 0.025 | 23.52 | 2.98 | 56.21
30 | 0.15 | 0 | 0.02 | 0.03 | 23.3 | 2.975 | 56.17
35 | 0.14 | 0 | 0.01 | 0.035 | 23.73 | 2.97 | 56.17
40 | 0.14 | 0 | 0.01 | 0.04 | 23.95 | 2.965 | 56.13
45 | 0.14 | 0 | 0.01 | 0.045 | 25.16 | 2.96 | 56.1
50 | 0.13 | 0 | 0 | 0.05 | 25.44 | 2.955 | 56.07
55 | 0.16 | 0 | 0.03 | 0.055 | 26.19 | 2.95 | 56.1
60 | 0.15 | 0 | 0.02 | 0.06 | 26.88 | 2.945 | 56.01
65 | 0.13 | 0 | 0 | 0.065 | 28.75 | 2.94 | 56
70 | 0.1 | 0 | -0.03 | 0.07 | 28.83 | 2.935 | 56.01
75 | 0.1 | 0 | -0.03 | 0.075 | 27.89 | 2.93 | 55.98
80 | 0.11 | 0 | -0.02 | 0.08 | 27.89 | 2.925 | 55.92
85 | 0.12 | 0 | -0.01 | 0.085 | 29.54 | 2.92 | 55.89
90 | 0.11 | 0 | -0.02 | 0.09 | 30.08 | 2.915 | 55.87
95 | 0.14 | 0 | 0.01 | 0.095 | 31.03 | 2.91 | 55.88
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
