bluepylons/Open-Switch-Curve-Meter/Force curves/Okay-I'm-Just-Going-to-Calibrate-Every-Day-Now/Tecsee-Blue-Velvet-Stem-Lavender-Housing-Measurement-II.ods

Raw data |  |  |  | Corrected Downstroke |  | Corrected Upstroke
X (microns) | Force (gf) | Actuated? | Tared | X (mm) | Force (gf) | X (mm) | Force (gf)
0 | -0.28 | 0
5 | -0.28 | 0
10 | 1.09 | 0
15 | 7.34 | 0
20 | 17.07 | 0
25 | 17.24 | 0
30 | 17.23 | 0
35 | 18.41 | 0
40 | 21.43 | 0
45 | 22.67 | 0
50 | 23.71 | 0
55 | 23.55 | 0
60 | 23.92 | 0
65 | 25.16 | 0
70 | 25.92 | 0
75 | 27.69 | 0
80 | 28.81 | 0
85 | 30.23 | 0
90 | 30.81 | 0
95 | 31.54 | 0
100 | 31.82 | 0
105 | 31.67 | 0
110 | 31.77 | 0
115 | 31.71 | 0
120 | 31.7 | 0
125 | 31.77 | 0
130 | 31.82 | 0
135 | 31.76 | 0
140 | 31.84 | 0
145 | 31.86 | 0
150 | 31.86 | 0
155 | 31.74 | 0
160 | 31.73 | 0
165 | 31.58 | 0
170 | 31.44 | 0
175 | 31.43 | 0
180 | 31.71 | 0
185 | 31.76 | 0
190 | 32.01 | 0
195 | 32.07 | 0
200 | 32.42 | 0
205 | 32.47 | 0
210 | 32.5 | 0
215 | 32.5 | 0
220 | 32.69 | 0
225 | 32.67 | 0
230 | 32.58 | 0
235 | 32.56 | 0
240 | 32.67 | 0
245 | 32.68 | 0
250 | 32.67 | 0
255 | 32.75 | 0
260 | 32.85 | 0
265 | 32.72 | 0
270 | 32.75 | 0
275 | 32.72 | 0 |  |  |  |  |  | Actuation
280 | 32.76 | 0 |  |  |  |  |  |  | 41
285 | 32.8 | 0 |  |  |  |  |  |  | 51
290 | 32.8 | 0
295 | 32.75 | 0 |  |  |  |  |  | Release
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
