bluepylons/Open-Switch-Curve-Meter/Force curves/Okay-I'm-Just-Going-to-Calibrate-Every-Day-Now/Durock-T1-stem-in-Harimau-housing.ods

Raw data |  |  |  | Corrected Downstroke |  | Corrected Upstroke
X (microns) | Force (gf) | Actuated? | Tared | X (mm) | Force (gf) | X (mm) | Force (gf)
0 | -0.13 | 0 | -0.02 | 0 | 0.72 | 3.895 | 74.53
5 | -0.12 | 0 | -0.01 | 0.005 | 3.64 | 3.89 | 68.44
10 | -0.1 | 0 | 0.01 | 0.01 | 16.98 | 3.885 | 63.83
15 | -0.1 | 0 | 0.01 | 0.015 | 24.13 | 3.88 | 63.89
20 | -0.12 | 0 | -0.01 | 0.02 | 35.01 | 3.875 | 63.57
25 | -0.09 | 0 | 0.02 | 0.025 | 36.32 | 3.87 | 63.69
30 | -0.09 | 0 | 0.02 | 0.03 | 36.93 | 3.865 | 63.37
35 | -0.1 | 0 | 0.01 | 0.035 | 37.18 | 3.86 | 63.51
40 | -0.11 | 0 | 0 | 0.04 | 38.1 | 3.855 | 63.47
45 | -0.11 | 0 | 0 | 0.045 | 38.62 | 3.85 | 63.58
50 | -0.1 | 0 | 0.01 | 0.05 | 39.69 | 3.845 | 63.42
55 | -0.09 | 0 | 0.02 | 0.055 | 39.95 | 3.84 | 63.55
60 | -0.12 | 0 | -0.01 | 0.06 | 40.5 | 3.835 | 63.5
65 | -0.1 | 0 | 0.01 | 0.065 | 41.13 | 3.83 | 63.64
70 | -0.11 | 0 | 0 | 0.07 | 41.7 | 3.825 | 63.61
75 | -0.12 | 0 | -0.01 | 0.075 | 42.33 | 3.82 | 63.88
80 | -0.12 | 0 | -0.01 | 0.08 | 42.55 | 3.815 | 63.84
85 | -0.08 | 0 | 0.03 | 0.085 | 42.86 | 3.81 | 63.81
90 | -0.11 | 0 | 0 | 0.09 | 43.05 | 3.805 | 63.76
95 | -0.09 | 0 | 0.02 | 0.095 | 43.05 | 3.8 | 63.68
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
