bluepylons/Open-Switch-Curve-Meter/Force curves/Okay-I'm-Just-Going-to-Calibrate-Every-Day-Now/Durock-T1.ods

Raw data |  |  |  | Corrected Downstroke |  | Corrected Upstroke
X (microns) | Force (gf) | Actuated? | Tared | X (mm) | Force (gf) | X (mm) | Force (gf)
0 | -0.02 | 0 | 0.01 | 0 | 8.18 | 3.89 | 89.67
5 | -0.03 | 0 | 0 | 0.005 | 21.53 | 3.885 | 77.07
10 | -0.05 | 0 | -0.02 | 0.01 | 28.17 | 3.88 | 71.03
15 | -0.06 | 0 | -0.03 | 0.015 | 38.72 | 3.875 | 63.51
20 | -0.05 | 0 | -0.02 | 0.02 | 41.55 | 3.87 | 63.14
25 | -0.01 | 0 | 0.02 | 0.025 | 42.72 | 3.865 | 63.06
30 | -0.02 | 0 | 0.01 | 0.03 | 43.15 | 3.86 | 63.4
35 | -0.01 | 0 | 0.02 | 0.035 | 42.88 | 3.855 | 63.27
40 | 0 | 0 | 0.03 | 0.04 | 43.29 | 3.85 | 63.56
45 | -0.04 | 0 | -0.01 | 0.045 | 43.33 | 3.845 | 63.5
50 | -0.02 | 0 | 0.01 | 0.05 | 43.42 | 3.84 | 63.98
55 | -0.04 | 0 | -0.01 | 0.055 | 43.34 | 3.835 | 63.93
60 | -0.04 | 0 | -0.01 | 0.06 | 43.66 | 3.83 | 64.03
65 | -0.03 | 0 | 0 | 0.065 | 43.83 | 3.825 | 64
70 | -0.03 | 0 | 0 | 0.07 | 43.97 | 3.82 | 63.99
75 | -0.03 | 0 | 0 | 0.075 | 44.15 | 3.815 | 63.9
80 | -0.03 | 0 | 0 | 0.08 | 44.81 | 3.81 | 63.87
85 | 0 | 0 | 0.03 | 0.085 | 44.81 | 3.805 | 63.76
90 | -0.06 | 0 | -0.03 | 0.09 | 44.97 | 3.8 | 63.69
95 | -0.06 | 0 | -0.03 | 0.095 | 44.99 | 3.795 | 63.67
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
