bluepylons/Open-Switch-Curve-Meter/Force curves/Okay-I'm-Just-Going-to-Calibrate-Every-Day-Now/Moyu-JWK-Queen.ods

Raw data |  |  |  | Corrected Downstroke |  | Corrected Upstroke
X (microns) | Force (gf) | Actuated? | Tared | X (mm) | Force (gf) | X (mm) | Force (gf)
0 | -0.29 | 0 | 0 | 0 | 1.72 | 3.885 | 83.45
5 | -0.31 | 0 | -0.02 | 0.005 | 8.09 | 3.88 | 79.6
10 | -0.3 | 0 | -0.01 | 0.01 | 23.98 | 3.875 | 71.79
15 | -0.28 | 0 | 0.01 | 0.015 | 30.5 | 3.87 | 69.65
20 | -0.27 | 0 | 0.02 | 0.02 | 36.95 | 3.865 | 68.35
25 | -0.28 | 0 | 0.01 | 0.025 | 37.63 | 3.86 | 68.11
30 | -0.3 | 0 | -0.01 | 0.03 | 38.26 | 3.855 | 68.01
35 | -0.28 | 0 | 0.01 | 0.035 | 39.82 | 3.85 | 67.78
40 | -0.28 | 0 | 0.01 | 0.04 | 40.59 | 3.845 | 67.7
45 | -0.25 | 0 | 0.04 | 0.045 | 41.16 | 3.84 | 67.49
50 | -0.27 | 0 | 0.02 | 0.05 | 41.4 | 3.835 | 67.44
55 | -0.31 | 0 | -0.02 | 0.055 | 41.97 | 3.83 | 67.33
60 | -0.27 | 0 | 0.02 | 0.06 | 42.35 | 3.825 | 67.22
65 | -0.29 | 0 | 0 | 0.065 | 43.24 | 3.82 | 67.13
70 | -0.31 | 0 | -0.02 | 0.07 | 43.69 | 3.815 | 67.03
75 | -0.3 | 0 | -0.01 | 0.075 | 43.81 | 3.81 | 66.92
80 | -0.3 | 0 | -0.01 | 0.08 | 43.74 | 3.805 | 66.83
85 | -0.28 | 0 | 0.01 | 0.085 | 43.78 | 3.8 | 66.67
90 | -0.28 | 0 | 0.01 | 0.09 | 43.85 | 3.795 | 66.57
95 | -0.27 | 0 | 0.02 | 0.095 | 43.88 | 3.79 | 66.44
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
