bluepylons/Open-Switch-Curve-Meter/Force curves/Okay-I'm-Just-Going-to-Calibrate-Every-Day-Now/Rebult-JWK-Harimau.ods

Raw data |  |  |  | Corrected Downstroke |  | Corrected Upstroke
X (microns) | Force (gf) | Actuated? | Tared | X (mm) | Force (gf) | X (mm) | Force (gf)
0 | -0.01 | 0 |  | 0 | 1.63 | 2.98 | 85.86
5 | -0.01 | 0 |  | 0.005 | 7.22 | 2.975 | 71.3
10 | -0.01 | 0 |  | 0.01 | 20.69 | 2.97 | 64.33
15 | -0.02 | 0 |  | 0.015 | 21.17 | 2.965 | 57.96
20 | -0.06 | 0 |  | 0.02 | 21.28 | 2.96 | 57.62
25 | -0.03 | 0 |  | 0.025 | 22.18 | 2.955 | 57.55
30 | 0 | 0 |  | 0.03 | 23.66 | 2.95 | 57.55
35 | -0.03 | 0 |  | 0.035 | 23.7 | 2.945 | 57.49
40 | -0.02 | 0 |  | 0.04 | 24.96 | 2.94 | 57.51
45 | -0.03 | 0 |  | 0.045 | 25.6 | 2.935 | 57.43
50 | -0.01 | 0 |  | 0.05 | 27.22 | 2.93 | 57.42
55 | -0.03 | 0 |  | 0.055 | 27.65 | 2.925 | 57.4
60 | -0.02 | 0 |  | 0.06 | 28.69 | 2.92 | 57.39
65 | -0.02 | 0 |  | 0.065 | 29.58 | 2.915 | 57.38
70 | -0.04 | 0 |  | 0.07 | 31.58 | 2.91 | 57.35
75 | -0.03 | 0 |  | 0.075 | 32.51 | 2.905 | 57.31
80 | -0.03 | 0 |  | 0.08 | 33.06 | 2.9 | 57.34
85 | -0.01 | 0 |  | 0.085 | 34.14 | 2.895 | 57.31
90 | -0.03 | 0 |  | 0.09 | 34.99 | 2.89 | 57.3
95 | 0.01 | 0 |  | 0.095 | 35.84 | 2.885 | 57.25
100 | 0 | 0 |  | 0.1 | 36.57 | 2.88 | 57.23
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
