bluepylons/Open-Switch-Curve-Meter/Force curves/Okay-I'm-Just-Going-to-Calibrate-Every-Day-Now/Rebult-JWK-Penyu.ods

Raw data |  |  |  | Corrected Downstroke |  | Corrected Upstroke
X (microns) | Force (gf) | Actuated? | Tared | X (mm) | Force (gf) | X (mm) | Force (gf)
0 | 0 | 0 |  | 0 | 0.4 | 2.935 | 131.8
5 | 0.01 | 0 |  | 0.005 | 9.85 | 2.93 | 119.19
10 | -0.01 | 0 |  | 0.01 | 13.73 | 2.925 | 111.74
15 | 0 | 0 |  | 0.015 | 16.92 | 2.92 | 96.36
20 | -0.02 | 0 |  | 0.02 | 17.59 | 2.915 | 88.61
25 | -0.02 | 0 |  | 0.025 | 19.38 | 2.91 | 72.74
30 | -0.02 | 0 |  | 0.03 | 18.83 | 2.905 | 65.08
35 | 0.02 | 0 |  | 0.035 | 18.07 | 2.9 | 52.42
40 | 0.01 | 0 |  | 0.04 | 18.16 | 2.895 | 50.65
45 | 0 | 0 |  | 0.045 | 18.33 | 2.89 | 50.07
50 | 0.01 | 0 |  | 0.05 | 20.4 | 2.885 | 49.99
55 | -0.03 | 0 |  | 0.055 | 23.31 | 2.88 | 49.91
60 | -0.01 | 0 |  | 0.06 | 24.25 | 2.875 | 49.95
65 | -0.02 | 0 |  | 0.065 | 25.16 | 2.87 | 49.92
70 | 0.01 | 0 |  | 0.07 | 25.67 | 2.865 | 49.85
75 | -0.01 | 0 |  | 0.075 | 26.75 | 2.86 | 49.83
80 | -0.01 | 0 |  | 0.08 | 27.57 | 2.855 | 49.68
85 | -0.01 | 0 |  | 0.085 | 27.56 | 2.85 | 49.71
90 | 0.03 | 0 |  | 0.09 | 27.61 | 2.845 | 49.62
95 | 0.02 | 0 |  | 0.095 | 28.26 | 2.84 | 49.61
100 | 0.4 | 0 |  | 0.1 | 29.72 | 2.835 | 49.57
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
