bluepylons/Open-Switch-Curve-Meter/Force curves/Okay-I'm-Just-Going-to-Calibrate-Every-Day-Now/Gateron-Cap-Yellow.ods

Raw data |  |  |  | Corrected Downstroke |  | Corrected Upstroke
X (microns) | Force (gf) | Actuated? | Tared | X (mm) | Force (gf) | X (mm) | Force (gf)
0 | 0.07 | 0 | 0.02 | 0 | 2.04 | 3.985 | 122.73
5 | 0.06 | 0 | 0.01 | 0.005 | 8.98 | 3.98 | 115.84
10 | 0.05 | 0 | 0 | 0.01 | 25.43 | 3.975 | 100.06
15 | 0.05 | 0 | 0 | 0.015 | 33.28 | 3.97 | 91.29
20 | 0.08 | 0 | 0.03 | 0.02 | 39.85 | 3.965 | 74.43
25 | 0.08 | 0 | 0.03 | 0.025 | 40.02 | 3.96 | 59.91
30 | 0.06 | 0 | 0.01 | 0.03 | 39.66 | 3.955 | 56.9
35 | 0.07 | 0 | 0.02 | 0.035 | 39.6 | 3.95 | 56.73
40 | 0.07 | 0 | 0.02 | 0.04 | 39.6 | 3.945 | 56.66
45 | 2.09 | 0 | 2.04 | 0.045 | 39.54 | 3.94 | 56.06
50 | 9.03 | 0 | 8.98 | 0.05 | 39.43 | 3.935 | 55.97
55 | 25.48 | 0 | 25.43 | 0.055 | 39.43 | 3.93 | 55.93
60 | 33.33 | 0 | 33.28 | 0.06 | 39.48 | 3.925 | 55.93
65 | 39.9 | 0 | 39.85 | 0.065 | 39.45 | 3.92 | 55.81
70 | 40.07 | 0 | 40.02 | 0.07 | 39.36 | 3.915 | 55.54
75 | 39.71 | 0 | 39.66 | 0.075 | 39.15 | 3.91 | 55.09
80 | 39.65 | 0 | 39.6 | 0.08 | 39.26 | 3.905 | 54.84
85 | 39.65 | 0 | 39.6 | 0.085 | 39.11 | 3.9 | 54.48
90 | 39.59 | 0 | 39.54 | 0.09 | 39.1 | 3.895 | 54.45
95 | 39.48 | 0 | 39.43 | 0.095 | 38.85 | 3.89 | 54.44
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
