bluepylons/Open-Switch-Curve-Meter/Force curves/Okay-I'm-Just-Going-to-Calibrate-Every-Day-Now/Gateron-Ink-Yellow.ods

Raw data |  |  |  | Corrected Downstroke |  | Corrected Upstroke
X (microns) | Force (gf) | Actuated? | Tared | X (mm) | Force (gf) | X (mm) | Force (gf)
0 | 0.09 | 0 | -0.02 | 0 | 0.3 | 3.325 | 109.15
5 | 0.11 | 0 | 0 | 0.005 | 10.25 | 3.32 | 100.11
10 | 0.11 | 0 | 0 | 0.01 | 16.16 | 3.315 | 95.98
15 | 0.1 | 0 | -0.01 | 0.015 | 19.59 | 3.31 | 88.37
20 | 0.09 | 0 | -0.02 | 0.02 | 19.96 | 3.305 | 85.26
25 | 0.13 | 0 | 0.02 | 0.025 | 20.46 | 3.3 | 79
30 | 0.12 | 0 | 0.01 | 0.03 | 20.4 | 3.295 | 75.98
35 | 0.12 | 0 | 0.01 | 0.035 | 20.15 | 3.29 | 69.36
40 | 0.11 | 0 | 0 | 0.04 | 19.85 | 3.285 | 66.15
45 | 0.13 | 0 | 0.02 | 0.045 | 19.93 | 3.28 | 62.23
50 | 0.13 | 0 | 0.02 | 0.05 | 19.92 | 3.275 | 61.73
55 | 0.13 | 0 | 0.02 | 0.055 | 20.15 | 3.27 | 61.67
60 | 0.15 | 0 | 0.04 | 0.06 | 19.86 | 3.265 | 61.6
65 | 0.13 | 0 | 0.02 | 0.065 | 19.61 | 3.26 | 61.57
70 | 0.1 | 0 | -0.01 | 0.07 | 23.2 | 3.255 | 61.49
75 | 0.12 | 0 | 0.01 | 0.075 | 28.26 | 3.25 | 61.48
80 | 0.1 | 0 | -0.01 | 0.08 | 34.23 | 3.245 | 61.42
85 | 0.08 | 0 | -0.03 | 0.085 | 34.38 | 3.24 | 61.41
90 | 0.14 | 0 | 0.03 | 0.09 | 34.28 | 3.235 | 61.31
95 | 0.14 | 0 | 0.03 | 0.095 | 34.4 | 3.23 | 61.27
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
