bluepylons/Open-Switch-Curve-Meter/Force curves/Okay-I'm-Just-Going-to-Calibrate-Every-Day-Now/Gazzew-Bobagum-52g.ods

Raw data |  |  |  | Corrected Downstroke |  | Corrected Upstroke
X (microns) | Force (gf) | Actuated? | Tared | X (mm) | Force (gf) | X (mm) | Force (gf)
0 | 0.16 | 0 | 0 | 0 | 8.9 | 3.235 | 113.88
5 | 0.15 | 0 | -0.01 | 0.005 | 11.97 | 3.23 | 110.69
10 | 0.13 | 0 | -0.03 | 0.01 | 15.14 | 3.225 | 108.71
15 | 0.18 | 0 | 0.02 | 0.015 | 17.32 | 3.22 | 104.63
20 | 0.17 | 0 | 0.01 | 0.02 | 18.51 | 3.215 | 102.6
25 | 0.16 | 0 | 0 | 0.025 | 20.7 | 3.21 | 98.61
30 | 0.16 | 0 | 0 | 0.03 | 21.89 | 3.205 | 96.67
35 | 0.18 | 0 | 0.02 | 0.035 | 23.02 | 3.2 | 92.55
40 | 0.19 | 0 | 0.03 | 0.04 | 23.04 | 3.195 | 90.62
45 | 0.18 | 0 | 0.02 | 0.045 | 23.62 | 3.19 | 86.96
50 | 0.16 | 0 | 0 | 0.05 | 23.99 | 3.185 | 85.24
55 | 0.15 | 0 | -0.01 | 0.055 | 24.25 | 3.18 | 81.72
60 | 0.18 | 0 | 0.02 | 0.06 | 24.05 | 3.175 | 80.08
65 | 0.19 | 0 | 0.03 | 0.065 | 23.25 | 3.17 | 76.75
70 | 0.17 | 0 | 0.01 | 0.07 | 23.3 | 3.165 | 75.21
75 | 0.17 | 0 | 0.01 | 0.075 | 23.39 | 3.16 | 72.09
80 | 0.14 | 0 | -0.02 | 0.08 | 23.53 | 3.155 | 69.22
85 | 0.14 | 0 | -0.02 | 0.085 | 23.62 | 3.15 | 67.81
90 | 0.15 | 0 | -0.01 | 0.09 | 23.63 | 3.145 | 65.88
95 | 0.17 | 0 | 0.01 | 0.095 | 23.51 | 3.14 | 65.13
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
