bluepylons/Open-Switch-Curve-Meter/Force curves/Okay-I'm-Just-Going-to-Calibrate-Every-Day-Now/KTT-Strawberry.ods

Raw data |  |  |  | Corrected Downstroke |  | Corrected Upstroke
X (microns) | Force (gf) | Actuated? | Tared | X (mm) | Force (gf) | X (mm) | Force (gf)
0 | -0.04 | 0 | 0 | 0 | 2.48 | 3.695 | 119.09
5 | -0.02 | 0 | 0.02 | 0.005 | 7.67 | 3.69 | 111.08
10 | -0.04 | 0 | 0 | 0.01 | 19.89 | 3.685 | 94.7
15 | -0.06 | 0 | -0.02 | 0.015 | 24.98 | 3.68 | 86.24
20 | -0.04 | 0 | 0 | 0.02 | 28.87 | 3.675 | 70.38
25 | -0.03 | 0 | 0.01 | 0.025 | 29.97 | 3.67 | 64.97
30 | -0.03 | 0 | 0.01 | 0.03 | 30.12 | 3.665 | 61.85
35 | -0.02 | 0 | 0.02 | 0.035 | 30.03 | 3.66 | 61.68
40 | -0.05 | 0 | -0.01 | 0.04 | 30.06 | 3.655 | 61.49
45 | -0.03 | 0 | 0.01 | 0.045 | 30.14 | 3.65 | 61.39
50 | -0.03 | 0 | 0.01 | 0.05 | 30.27 | 3.645 | 61.26
55 | -0.05 | 0 | -0.01 | 0.055 | 30.36 | 3.64 | 61.12
60 | -0.08 | 0 | -0.04 | 0.06 | 30.44 | 3.635 | 61.04
65 | -0.04 | 0 | 0 | 0.065 | 30.43 | 3.63 | 60.93
70 | -0.03 | 0 | 0.01 | 0.07 | 30.51 | 3.625 | 60.85
75 | -0.04 | 0 | 0 | 0.075 | 30.68 | 3.62 | 60.75
80 | -0.02 | 0 | 0.02 | 0.08 | 30.79 | 3.615 | 60.73
85 | -0.07 | 0 | -0.03 | 0.085 | 30.69 | 3.61 | 60.62
90 | -0.07 | 0 | -0.03 | 0.09 | 30.76 | 3.605 | 60.56
95 | -0.07 | 0 | -0.03 | 0.095 | 30.9 | 3.6 | 60.48
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
