bluepylons/Open-Switch-Curve-Meter/Force curves/Okay-I'm-Just-Going-to-Calibrate-Every-Day-Now/Momoka-Frog.ods

Raw data |  |  |  | Corrected Downstroke |  | Corrected Upstroke
X (microns) | Force (gf) | Actuated? | Tared | X (mm) | Force (gf) | X (mm) | Force (gf)
0 | -0.07 | 0 | -0.02 | 0 | 0.62 | 4.05 | 97.94
5 | -0.08 | 0 | -0.03 | 0.005 | 3.17 | 4.045 | 91.34
10 | -0.06 | 0 | -0.01 | 0.01 | 12.51 | 4.04 | 79.84
15 | -0.05 | 0 | 0 | 0.015 | 17.44 | 4.035 | 74.13
20 | -0.08 | 0 | -0.03 | 0.02 | 21.01 | 4.03 | 65.3
25 | -0.08 | 0 | -0.03 | 0.025 | 21.5 | 4.025 | 62.42
30 | -0.05 | 0 | 0 | 0.03 | 21.44 | 4.02 | 59.97
35 | -0.05 | 0 | 0 | 0.035 | 22.07 | 4.015 | 59.52
40 | -0.07 | 0 | -0.02 | 0.04 | 22.96 | 4.01 | 59.18
45 | -0.08 | 0 | -0.03 | 0.045 | 28.09 | 4.005 | 59.17
50 | -0.05 | 0 | 0 | 0.05 | 29.69 | 4 | 59.07
55 | -0.06 | 0 | -0.01 | 0.055 | 30.91 | 3.995 | 59.03
60 | -0.05 | 0 | 0 | 0.06 | 31.25 | 3.99 | 58.96
65 | -0.04 | 0 | 0.01 | 0.065 | 31.92 | 3.985 | 58.89
70 | -0.03 | 0 | 0.02 | 0.07 | 32.18 | 3.98 | 58.84
75 | -0.06 | 0 | -0.01 | 0.075 | 32.58 | 3.975 | 58.8
80 | -0.03 | 0 | 0.02 | 0.08 | 32.69 | 3.97 | 58.79
85 | -0.02 | 0 | 0.03 | 0.085 | 32.96 | 3.965 | 58.8
90 | -0.01 | 0 | 0.04 | 0.09 | 32.95 | 3.96 | 58.78
95 | -0.01 | 0 | 0.04 | 0.095 | 32.91 | 3.955 | 58.75
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
