bluepylons/Open-Switch-Curve-Meter/Force curves/Okay-I'm-Just-Going-to-Calibrate-Every-Day-Now/Polia-vs-Halo-vs-U4T-in-Boba.ods

Raw data (U4T) |  |  |  | Raw data (Polia) |  |  |  | Raw data (Halo) |  |  |  | Corrected Downstroke |  | Corrected Upstroke (U4T) |  | Corrected Downstroke |  | Corrected Upstroke (Polia) |  | Corrected Downstroke |  | Corrected Upstroke (Halo)
X (microns) | Force (gf) | Actuated? | Tared | X (microns) | Force (gf) | Actuated? | Tared | X (microns) | Force (gf) | Actuated? | Tared | X (mm) | Force (gf) | X (mm) | Force (gf) | X (mm) | Force (gf) | X (mm) | Force (gf) | X (mm) | Force (gf) | X (mm) | Force (gf)
0 | -0.02 | 0 | 0 | 0 | -0.17 | 0 | 0 | 0 | -0.16 | 0 | -0.03 | 0 | 0.09 | 3.105 | 121.1 | 0 | 0.15 | 3.225 | 113.76 | 0 | 0.28 | 3.28 | 115.92
5 | -0.03 | 0 | -0.01 | 5 | -0.13 | 0 | 0.04 | 5 | -0.14 | 0 | -0.01 | 0.005 | 7.3 | 3.1 | 101.54 | 0.005 | 10.65 | 3.22 | 104.53 | 0.005 | 3 | 3.275 | 106.44
10 | -0.02 | 0 | 0 | 10 | -0.12 | 0 | 0.05 | 10 | -0.13 | 0 | 0 | 0.01 | 16.7 | 3.095 | 82.8 | 0.01 | 17.96 | 3.215 | 86.16 | 0.01 | 16.11 | 3.27 | 87.66
15 | -0.02 | 0 | 0 | 15 | -0.12 | 0 | 0.05 | 15 | -0.16 | 0 | -0.03 | 0.015 | 33.45 | 3.09 | 73.69 | 0.015 | 31.54 | 3.21 | 69.77 | 0.015 | 30.62 | 3.265 | 78.55
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
