bluepylons/Open-Switch-Curve-Meter/Force curves/Okay-I'm-Just-Going-to-Calibrate-Every-Day-Now/Kailh-Polia-Stem-Zealio-V2-Bottom-Cherry-Top.ods

Raw data |  |  |  | Corrected Downstroke |  | Corrected Upstroke
X (microns) | Force (gf) | Actuated? | Tared | X (mm) | Force (gf) | X (mm) | Force (gf)
0 | 0.01 | 0 |  | 0 | 0.17 | 3.16 | 94.52
5 | 0.02 | 0 |  | 0.005 | 8.53 | 3.155 | 90.68
10 | 0.01 | 0 |  | 0.01 | 18.43 | 3.15 | 79.29
15 | 0.02 | 0 |  | 0.015 | 20.66 | 3.145 | 73.47
20 | 0.03 | 0 |  | 0.02 | 22.49 | 3.14 | 62.81
25 | 0.02 | 0 |  | 0.025 | 22.88 | 3.135 | 58.73
30 | 0.08 | 0 |  | 0.03 | 23.18 | 3.13 | 55.42
35 | 0.05 | 0 |  | 0.035 | 23.31 | 3.125 | 55.24
40 | 0.05 | 0 |  | 0.04 | 23.61 | 3.12 | 55.18
45 | 0.04 | 0 |  | 0.045 | 23.58 | 3.115 | 55.15
50 | 0.05 | 0 |  | 0.05 | 23.81 | 3.11 | 55.05
55 | 0.04 | 0 |  | 0.055 | 24.33 | 3.105 | 55
60 | 0.05 | 0 |  | 0.06 | 25.18 | 3.1 | 54.92
65 | 0.17 | 0 |  | 0.065 | 25.5 | 3.095 | 54.85
70 | 8.53 | 0 |  | 0.07 | 26.07 | 3.09 | 54.68
75 | 18.43 | 0 |  | 0.075 | 26.32 | 3.085 | 54.6
80 | 20.66 | 0 |  | 0.08 | 26.98 | 3.08 | 54.48
85 | 22.49 | 0 |  | 0.085 | 27.89 | 3.075 | 54.33
90 | 22.88 | 0 |  | 0.09 | 28.45 | 3.07 | 54.26
95 | 23.18 | 0 |  | 0.095 | 29.44 | 3.065 | 54.1
100 | 23.31 | 0 |  | 0.1 | 29.79 | 3.06 | 54.06
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
