bluepylons/Open-Switch-Curve-Meter/Force curves/April-10-21-calibration/Blank-template.ods

Raw data |  |  | Corrected Downstroke |  | Corrected Upstroke
X (microns) | Force (gf) | Actuated? | X (mm) | Force (gf) | X (mm) | Force (gf)
 |  |  |  |  |  |  | Actuation
 |  |  |  |  |  |  |  | 40
 |  |  |  |  |  |  |  | 60
 |  |  |  |  |  |  | Release
 |  |  |  |  |  |  |  | 3
 |  |  |  |  |  |  |  | 23
