bluepylons/Open-Switch-Curve-Meter/Force curves/April-10-21-calibration/Cherry-MX-Blue-stem-in-Koala.ods

Raw data |  |  | Corrected Downstroke |  | Corrected Upstroke
X (microns) | Force (gf) | Actuated? | X (mm) | Force (gf) | X (mm) | Force (gf)
0 | -0.15 | 0 | 0 | 1.73 | 3.27 | 61.72
5 | -0.16 | 0 | 0.005 | 7.39 | 3.265 | 61.44
10 | -0.15 | 0 | 0.01 | 21.19 | 3.26 | 61.12
15 | -0.16 | 0 | 0.015 | 24.78 | 3.255 | 60.81
20 | -0.17 | 0 | 0.02 | 26.42 | 3.25 | 60.44
25 | -0.18 | 0 | 0.025 | 27.72 | 3.245 | 60.11
30 | -0.15 | 0 | 0.03 | 28.09 | 3.24 | 59.74
35 | -0.15 | 0 | 0.035 | 28.42 | 3.235 | 59.94
40 | -0.17 | 0 | 0.04 | 28.4 | 3.23 | 59.9
45 | -0.16 | 0 | 0.045 | 28.31 | 3.225 | 59.94
50 | -0.16 | 0 | 0.05 | 28.37 | 3.22 | 59.93
55 | -0.14 | 0 | 0.055 | 28.43 | 3.215 | 60.11
60 | -0.14 | 0 | 0.06 | 28.38 | 3.21 | 60.28
65 | -0.14 | 0 | 0.065 | 28.44 | 3.205 | 60.38
70 | -0.15 | 0 | 0.07 | 28.96 | 3.2 | 60.39
75 | -0.15 | 0 | 0.075 | 29.22 | 3.195 | 60.38
80 | -0.16 | 0 | 0.08 | 29.54 | 3.19 | 60.35
85 | -0.17 | 0 | 0.085 | 29.78 | 3.185 | 60.29
90 | -0.2 | 0 | 0.09 | 30.03 | 3.18 | 60.15
95 | -0.21 | 0 | 0.095 | 30.56 | 3.175 | 60.21
100 | -0.18 | 0 | 0.1 | 30.71 | 3.17 | 60.14
105 | -0.16 | 0 | 0.105 | 31.03 | 3.165 | 60.15
110 | -0.18 | 0 | 0.11 | 31.23 | 3.16 | 60.01
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
