bluepylons/Open-Switch-Curve-Meter/Force curves/April-10-21-calibration/Cherry-MX-Clear-slow-vs-fast.ods

MX Clear with Kailh Speed Pale Blue spring |  | Cherry MX Clear |  | Kailh Speed Pale Blue (just spring) |  | MX Clear (just spring) |  | Kailh Speed Pale Blue (downstroke) |  | Kailh Speed Pale Blue (upstroke) |  | Cherry MX Clear (downstroke) |  | Cherry MX Clear (upstroke) |  | Kailh Speed Pale Blue (spring only) |  | Cherry MX Clear (spring only)
X (microns) | Force (gf) | X (microns) | Force (gf) | X (microns) | Force (gf) | X (microns) | Force (gf) | X (mm) | Force (gf) | X (mm) | Force (gf) | X (mm) | Force (gf) | X (mm) | Force (gf) | X (mm) | Force (gf) | X (mm) | Force (gf)
0 | 0.2 | 0 | 0.3 | 0 | 0.18 | 0 | 0.34 | 0 | 4.05 | 3.97 | 92.58 | 0 | 0.78 |  |  | 0 | 0.3 | 0 | 0.63
5 | 0.2 | 5 | 0.3 | 5 | 0.19 | 5 | 0.33 | 0.005 | 17.4 | 3.965 | 89.35 | 0.005 | 5.12 |  |  | 0.005 | 1.14 | 0.005 | 10.85
10 | 0.19 | 10 | 0.3 | 10 | 0.16 | 10 | 0.33 | 0.01 | 24.9 | 3.96 | 89.1 | 0.01 | 18.47 |  |  | 0.01 | 13.86 | 0.01 | 18.15
15 | 0.2 | 15 | 0.3 | 15 | 0.17 | 15 | 0.31 | 0.015 | 32.01 | 3.955 | 88.87 | 0.015 | 22.57 |  |  | 0.015 | 21.95 | 0.015 | 26.27
20 | 0.23 | 20 | 0.3 | 20 | 0.17 | 20 | 0.32 | 0.02 | 33.71 | 3.95 | 88.99 | 0.02 | 23.57 | ` |  | 0.02 | 34.88 | 0.02 | 26.74
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
