bluepylons/Open-Switch-Curve-Meter/Force curves/April-10-21-calibration/Cherry-MX-Clear-stem-in-Cherry-MX-Blue.ods

Raw data |  |  | Corrected Downstroke |  | Corrected Upstroke
X (microns) | Force (gf) | Actuated? | X (mm) | Force (gf) | X (mm) | Force (gf)
0 | -0.81 | 0 | 0 | 2.02 | 4.02 | 87.89
5 | -0.81 | 0 | 0.005 | 16.11 | 4.015 | 86.28
10 | -0.83 | 0 | 0.01 | 20.77 | 4.01 | 86.14
15 | -0.84 | 0 | 0.015 | 24.64 | 4.005 | 86.1
20 | -0.81 | 0 | 0.02 | 26.03 | 4 | 85.86
25 | -0.82 | 0 | 0.025 | 27.38 | 3.995 | 85.78
30 | -0.8 | 0 | 0.03 | 29.53 | 3.99 | 85.74
35 | -0.82 | 0 | 0.035 | 30.21 | 3.985 | 85.81
40 | -0.84 | 0 | 0.04 | 31.26 | 3.98 | 85.81
45 | -0.81 | 0 | 0.045 | 31.08 | 3.975 | 85.76
50 | -0.82 | 0 | 0.05 | 30.4 | 3.97 | 85.66
55 | -0.8 | 0 | 0.055 | 30.22 | 3.965 | 85.36
60 | -0.8 | 0 | 0.06 | 30.21 | 3.96 | 85.18
65 | -0.82 | 0 | 0.065 | 30.36 | 3.955 | 85.01
70 | -0.78 | 0 | 0.07 | 30.6 | 3.95 | 84.95
75 | -0.8 | 0 | 0.075 | 30.93 | 3.945 | 84.88
80 | -0.83 | 0 | 0.08 | 31.02 | 3.94 | 84.68
85 | -0.86 | 0 | 0.085 | 31.03 | 3.935 | 84.66
90 | -0.81 | 0 | 0.09 | 31.07 | 3.93 | 84.57
95 | -0.83 | 0 | 0.095 | 31.14 | 3.925 | 84.54
100 | -0.83 | 0 | 0.1 | 31.25 | 3.92 | 84.54
105 | -0.85 | 0 | 0.105 | 31.26 | 3.915 | 84.31
110 | -0.85 | 0 | 0.11 | 31.44 | 3.91 | 84.18
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
