bluepylons/Open-Switch-Curve-Meter/Force curves/April-10-21-calibration/Durock-T1-stem-in-Durock-Medium-Tactile-housing.ods

Raw data |  |  | Corrected Downstroke |  | Corrected Upstroke
X (microns) | Force (gf) | Actuated? | X (mm) | Force (gf) | X (mm) | Force (gf)
0 | -0.65 | 0 | 0 | 0 | 3.805 | 64
5 | -0.66 | 0 | 0.005 | 3.91 | 3.8 | 63.95
10 | -0.67 | 0 | 0.01 | 10.92 | 3.795 | 63.92
15 | -0.68 | 0 | 0.015 | 28.59 | 3.79 | 63.9
20 | -0.66 | 0 | 0.02 | 34.22 | 3.785 | 63.89
25 | -0.64 | 0 | 0.025 | 36.45 | 3.78 | 63.87
30 | -0.66 | 0 | 0.03 | 36.01 | 3.775 | 63.78
35 | -0.67 | 0 | 0.035 | 35.59 | 3.77 | 63.7
40 | -0.68 | 0 | 0.04 | 35.42 | 3.765 | 63.62
45 | -0.68 | 0 | 0.045 | 35.44 | 3.76 | 63.61
50 | -0.65 | 0 | 0.05 | 35.15 | 3.755 | 63.59
55 | -0.68 | 0 | 0.055 | 35.09 | 3.75 | 63.6
60 | -0.66 | 0 | 0.06 | 35.7 | 3.745 | 63.59
65 | -0.67 | 0 | 0.065 | 36.48 | 3.74 | 63.52
70 | -0.65 | 0 | 0.07 | 36.83 | 3.735 | 63.5
75 | -0.68 | 0 | 0.075 | 36.93 | 3.73 | 63.41
80 | -0.67 | 0 | 0.08 | 37.15 | 3.725 | 63.39
85 | -0.66 | 0 | 0.085 | 39.3 | 3.72 | 63.35
90 | -0.69 | 0 | 0.09 | 41.34 | 3.715 | 63.26
95 | -0.67 | 0 | 0.095 | 43.91 | 3.71 | 63.21
100 | -0.69 | 0 | 0.1 | 44.1 | 3.705 | 63.15
105 | -0.7 | 0 | 0.105 | 44.22 | 3.7 | 63.13
110 | -0.69 | 0 | 0.11 | 44.13 | 3.695 | 63.07
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
