bluepylons/Open-Switch-Curve-Meter/Force curves/April-10-21-calibration/Durock-T1-stem-in-Kailh-Purple-housing.ods

Raw data |  |  | Corrected Downstroke |  | Corrected Upstroke
X (microns) | Force (gf) | Actuated? | X (mm) | Force (gf) | X (mm) | Force (gf)
0 | -0.84 | 0 | 0 | 0.52 | 3.96 | 71.9
5 | -0.82 | 0 | 0.005 | 8.07 | 3.955 | 71.78
10 | -0.8 | 0 | 0.01 | 25.89 | 3.95 | 71.72
15 | -0.81 | 0 | 0.015 | 30.47 | 3.945 | 71.53
20 | -0.8 | 0 | 0.02 | 32.52 | 3.94 | 71.45
25 | -0.82 | 0 | 0.025 | 34.05 | 3.935 | 71.38
30 | -0.84 | 0 | 0.03 | 34.45 | 3.93 | 71.22
35 | -0.83 | 0 | 0.035 | 34.39 | 3.925 | 71.12
40 | -0.81 | 0 | 0.04 | 34.3 | 3.92 | 71.06
45 | -0.79 | 0 | 0.045 | 33.92 | 3.915 | 70.99
50 | -0.79 | 0 | 0.05 | 33.81 | 3.91 | 70.96
55 | -0.85 | 0 | 0.055 | 34.01 | 3.905 | 70.95
60 | -0.82 | 0 | 0.06 | 34.48 | 3.9 | 71.05
65 | -0.82 | 0 | 0.065 | 34.41 | 3.895 | 71.14
70 | -0.82 | 0 | 0.07 | 33.99 | 3.89 | 71.14
75 | -0.85 | 0 | 0.075 | 33.89 | 3.885 | 71.07
80 | -0.82 | 0 | 0.08 | 34.47 | 3.88 | 71.03
85 | -0.84 | 0 | 0.085 | 34.9 | 3.875 | 70.9
90 | -0.8 | 0 | 0.09 | 35.06 | 3.87 | 70.82
95 | -0.82 | 0 | 0.095 | 35.01 | 3.865 | 70.77
100 | -0.81 | 0 | 0.1 | 35.57 | 3.86 | 70.68
105 | -0.81 | 0 | 0.105 | 36.73 | 3.855 | 70.64
110 | -0.83 | 0 | 0.11 | 37.12 | 3.85 | 70.52
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
