bluepylons/Open-Switch-Curve-Meter/Force curves/April-10-21-calibration/Feker-Holy-Panda-Stem-In-Durock-T1.ods

Raw data |  |  | Corrected Downstroke |  | Corrected Upstroke
X (microns) | Force (gf) | Actuated? | X (mm) | Force (gf) | X (mm) | Force (gf)
0 | 0.04 | 0 | 0 | 0.74 | 3 | 58.48
5 | 0.04 | 0 | 0.005 | 6.73 | 2.995 | 58.01
10 | 0.05 | 0 | 0.01 | 17.57 | 2.99 | 58.02
15 | 0.05 | 0 | 0.015 | 27.95 | 2.985 | 57.98
20 | 0.07 | 0 | 0.02 | 32.36 | 2.98 | 57.86
25 | 0.04 | 0 | 0.025 | 31.34 | 2.975 | 57.7
30 | 0.08 | 0 | 0.03 | 30.79 | 2.97 | 57.73
35 | 0.04 | 0 | 0.035 | 30.58 | 2.965 | 57.68
40 | 0.04 | 0 | 0.04 | 30.51 | 2.96 | 57.65
45 | 0.05 | 0 | 0.045 | 31.11 | 2.955 | 57.79
50 | 0.06 | 0 | 0.05 | 31.95 | 2.95 | 57.8
55 | 0.05 | 0 | 0.055 | 33.42 | 2.945 | 57.68
60 | 0.07 | 0 | 0.06 | 35.53 | 2.94 | 57.72
65 | 0.07 | 0 | 0.065 | 38.08 | 2.935 | 57.61
70 | 0.04 | 0 | 0.07 | 42.7 | 2.93 | 57.43
75 | 0.06 | 0 | 0.075 | 43.73 | 2.925 | 57.24
80 | 0.06 | 0 | 0.08 | 44.36 | 2.92 | 57.22
85 | 0.09 | 0 | 0.085 | 44.87 | 2.915 | 57.21
90 | 0.07 | 0 | 0.09 | 45.26 | 2.91 | 57.16
95 | 0.06 | 0 | 0.095 | 45.54 | 2.905 | 57.12
100 | 0.06 | 0 | 0.1 | 45.49 | 2.9 | 57.26
105 | 0.05 | 0 | 0.105 | 45.43 | 2.895 | 57.32
110 | 0.05 | 0 | 0.11 | 45.38 | 2.89 | 57.25
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
