bluepylons/Open-Switch-Curve-Meter/Force curves/April-10-21-calibration/Gateron-Yellow-leaf-vs-no-leaf.ods

Raw data | (with leaf) | Corrected Downstroke |  | Corrected Upstroke |  | Raw data | (no leaf) | Corrected Downstroke |  | Corrected Upstroke
X (microns) | Force (gf) | X (mm) | Force (gf) | X (mm) | Force (gf) | X (microns) | Force (gf) | X (mm) | Force (gf) | X (mm) | Force (gf)
0 | 0 | 0 | 1.58 | 3.985 | 86.66 | 0 | -0.13 | 0 | 0.03 | 4 | 102.26
5 | 0.02 | 0.005 | 8.42 | 3.98 | 76.27 | 5 | -0.11 | 0.005 | 2.14 | 3.995 | 80.25
10 | 0 | 0.01 | 18.19 | 3.975 | 68.91 | 10 | -0.13 | 0.01 | 15.39 | 3.99 | 71.06
15 | -0.02 | 0.015 | 26.99 | 3.97 | 64.85 | 15 | -0.12 | 0.015 | 22.12 | 3.985 | 66.03
20 | 0 | 0.02 | 32.14 | 3.965 | 64.53 | 20 | -0.13 | 0.02 | 29.39 | 3.98 | 64.82
25 | -0.01 | 0.025 | 32.97 | 3.96 | 64.33 | 25 | -0.12 | 0.025 | 34.47 | 3.975 | 64.25
30 | -0.05 | 0.03 | 32.89 | 3.955 | 64.2 | 30 | -0.13 | 0.03 | 35.41 | 3.97 | 63.65
35 | -0.05 | 0.035 | 32.94 | 3.95 | 64.06 | 35 | -0.13 | 0.035 | 36.03 | 3.965 | 63.59
40 | -0.02 | 0.04 | 32.97 | 3.945 | 63.88 | 40 | -0.16 | 0.04 | 36.33 | 3.96 | 63.54
45 | 0.05 | 0.045 | 33 | 3.94 | 63.81 | 45 | -0.16 | 0.045 | 36.37 | 3.955 | 63.5
50 | -0.01 | 0.05 | 33.05 | 3.935 | 63.72 | 50 | -0.14 | 0.05 | 36.37 | 3.95 | 63.44
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
