bluepylons/Open-Switch-Curve-Meter/Force curves/April-10-21-calibration/Gazzew-Phoenix-in-Boba.ods

Raw data |  |  | Corrected Downstroke |  | Corrected Upstroke
X (microns) | Force (gf) | Actuated? | X (mm) | Force (gf) | X (mm) | Force (gf)
0 | -0.57 | 0 | 0 | 4.73 | 3.85 | 68.75
5 | -0.53 | 0 | 0.005 | 18.25 | 3.845 | 68.66
10 | -0.54 | 0 | 0.01 | 30.87 | 3.84 | 68.6
15 | -0.54 | 0 | 0.015 | 36.69 | 3.835 | 68.58
20 | -0.57 | 0 | 0.02 | 40.96 | 3.83 | 68.57
25 | -0.55 | 0 | 0.025 | 41.31 | 3.825 | 68.5
30 | -0.53 | 0 | 0.03 | 42.36 | 3.82 | 68.46
35 | -0.56 | 0 | 0.035 | 42.99 | 3.815 | 68.48
40 | -0.57 | 0 | 0.04 | 43.91 | 3.81 | 68.49
45 | -0.58 | 0 | 0.045 | 44.62 | 3.805 | 68.45
50 | -0.55 | 0 | 0.05 | 45.3 | 3.8 | 68.43
55 | -0.53 | 0 | 0.055 | 45.58 | 3.795 | 68.39
60 | -0.53 | 0 | 0.06 | 45.36 | 3.79 | 68.38
65 | -0.53 | 0 | 0.065 | 45.43 | 3.785 | 68.43
70 | -0.56 | 0 | 0.07 | 45.43 | 3.78 | 68.39
75 | -0.55 | 0 | 0.075 | 45.51 | 3.775 | 68.37
80 | -0.52 | 0 | 0.08 | 45.22 | 3.77 | 68.33
85 | -0.55 | 0 | 0.085 | 45.56 | 3.765 | 68.31
90 | -0.54 | 0 | 0.09 | 45.34 | 3.76 | 68.26
95 | -0.54 | 0 | 0.095 | 45.05 | 3.755 | 68.16
100 | -0.57 | 0 | 0.1 | 44.66 | 3.75 | 68.13
105 | -0.57 | 0 | 0.105 | 44.96 | 3.745 | 68.05
110 | -0.56 | 0 | 0.11 | 45 | 3.74 | 68.04
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
