bluepylons/Open-Switch-Curve-Meter/Force curves/April-10-21-calibration/Gazzew-Phoenix-in-Sky.ods

Raw data |  |  | Corrected Downstroke |  | Corrected Upstroke
X (microns) | Force (gf) | Actuated? | X (mm) | Force (gf) | X (mm) | Force (gf)
0 | -0.53 | 0 | 0 | 0.69 | 3.785 | 63.74
5 | -0.55 | 0 | 0.005 | 11.86 | 3.78 | 63.74
10 | -0.51 | 0 | 0.01 | 19.19 | 3.775 | 63.71
15 | -0.51 | 0 | 0.015 | 28.8 | 3.77 | 63.68
20 | -0.53 | 0 | 0.02 | 30.24 | 3.765 | 63.61
25 | -0.51 | 0 | 0.025 | 30.29 | 3.76 | 63.59
30 | -0.53 | 0 | 0.03 | 30.19 | 3.755 | 63.49
35 | -0.54 | 0 | 0.035 | 30.24 | 3.75 | 63.47
40 | -0.53 | 0 | 0.04 | 30.32 | 3.745 | 63.42
45 | -0.55 | 0 | 0.045 | 30.36 | 3.74 | 63.36
50 | -0.53 | 0 | 0.05 | 30.41 | 3.735 | 63.31
55 | -0.54 | 0 | 0.055 | 30.6 | 3.73 | 63.27
60 | -0.53 | 0 | 0.06 | 30.81 | 3.725 | 63.24
65 | -0.56 | 0 | 0.065 | 30.91 | 3.72 | 63.21
70 | -0.54 | 0 | 0.07 | 31.07 | 3.715 | 63.12
75 | -0.56 | 0 | 0.075 | 31.21 | 3.71 | 63.09
80 | -0.57 | 0 | 0.08 | 31.29 | 3.705 | 63.05
85 | -0.52 | 0 | 0.085 | 31.28 | 3.7 | 63.05
90 | -0.53 | 0 | 0.09 | 31.39 | 3.695 | 63.03
95 | -0.52 | 0 | 0.095 | 32.9 | 3.69 | 63.06
100 | -0.51 | 0 | 0.1 | 33.95 | 3.685 | 63.05
105 | -0.35 | 0 | 0.105 | 35.99 | 3.68 | 62.98
110 | 0.69 | 0 | 0.11 | 36.96 | 3.675 | 62.97
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
