bluepylons/Open-Switch-Curve-Meter/Force curves/April-10-21-calibration/Gazzew-Phoenix-Stem-In-T1.ods

Raw data |  |  | Corrected Downstroke |  | Corrected Upstroke
X (microns) | Force (gf) | Actuated? | X (mm) | Force (gf) | X (mm) | Force (gf)
0 | -0.56 | 0 | 0 | 7.61 | 3.805 | 94.71
5 | -0.57 | 0 | 0.005 | 15.02 | 3.8 | 86.78
10 | -0.56 | 0 | 0.01 | 26.98 | 3.795 | 72.55
15 | -0.55 | 0 | 0.015 | 31.21 | 3.79 | 68.2
20 | -0.55 | 0 | 0.02 | 35.29 | 3.785 | 65.86
25 | -0.56 | 0 | 0.025 | 36.62 | 3.78 | 65.89
30 | -0.55 | 0 | 0.03 | 37.3 | 3.775 | 65.89
35 | -0.55 | 0 | 0.035 | 38.47 | 3.77 | 65.85
40 | -0.56 | 0 | 0.04 | 38.75 | 3.765 | 65.81
45 | -0.54 | 0 | 0.045 | 39.11 | 3.76 | 65.68
50 | -0.55 | 0 | 0.05 | 39.34 | 3.755 | 65.68
55 | -0.56 | 0 | 0.055 | 40.34 | 3.75 | 65.57
60 | -0.53 | 0 | 0.06 | 41.44 | 3.745 | 65.59
65 | -0.54 | 0 | 0.065 | 42.45 | 3.74 | 65.53
70 | -0.54 | 0 | 0.07 | 42.74 | 3.735 | 65.5
75 | -0.52 | 0 | 0.075 | 42.94 | 3.73 | 65.36
80 | -0.51 | 0 | 0.08 | 42.97 | 3.725 | 65.36
85 | -0.56 | 0 | 0.085 | 42.87 | 3.72 | 65.39
90 | -0.52 | 0 | 0.09 | 42.93 | 3.715 | 65.43
95 | -0.56 | 0 | 0.095 | 42.97 | 3.71 | 65.44
100 | -0.56 | 0 | 0.1 | 43.15 | 3.705 | 65.41
105 | -0.54 | 0 | 0.105 | 43.09 | 3.7 | 65.35
110 | -0.54 | 0 | 0.11 | 43.21 | 3.695 | 65.37
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
