bluepylons/Open-Switch-Curve-Meter/Force curves/April-10-21-calibration/Gazzew-U4-stem-in-Cherry-MX-Blue.ods

Raw data |  |  | Corrected Downstroke |  | Corrected Upstroke
X (microns) | Force (gf) | Actuated? | X (mm) | Force (gf) | X (mm) | Force (gf)
0 | -0.79 | 0 | 0 | 2.38 | 3.36 | 97.25
5 | -0.79 | 0 | 0.005 | 5.07 | 3.355 | 96.28
10 | -0.77 | 0 | 0.01 | 8.81 | 3.35 | 94.29
15 | -0.78 | 0 | 0.015 | 10.48 | 3.345 | 93.33
20 | -0.78 | 0 | 0.02 | 13.94 | 3.34 | 91.39
25 | -0.78 | 0 | 0.025 | 15.6 | 3.335 | 90.48
30 | -0.78 | 0 | 0.03 | 18.54 | 3.33 | 88.66
35 | -0.83 | 0 | 0.035 | 19.89 | 3.325 | 87.78
40 | -0.81 | 0 | 0.04 | 21.09 | 3.32 | 86.92
45 | -0.77 | 0 | 0.045 | 23.28 | 3.315 | 85.21
50 | -0.8 | 0 | 0.05 | 24.32 | 3.31 | 84.35
55 | -0.77 | 0 | 0.055 | 26.51 | 3.305 | 82.72
60 | -0.77 | 0 | 0.06 | 27.6 | 3.3 | 81.89
65 | -0.77 | 0 | 0.065 | 29.53 | 3.295 | 80.41
70 | -0.79 | 0 | 0.07 | 30.42 | 3.29 | 79.63
75 | -0.8 | 0 | 0.075 | 31.31 | 3.285 | 78.99
80 | -0.79 | 0 | 0.08 | 33.17 | 3.28 | 77.6
85 | -0.8 | 0 | 0.085 | 34.11 | 3.275 | 76.95
90 | -0.81 | 0 | 0.09 | 35.95 | 3.27 | 75.51
95 | -0.77 | 0 | 0.095 | 36.88 | 3.265 | 74.8
100 | -0.78 | 0 | 0.1 | 38.77 | 3.26 | 73.35
105 | -0.79 | 0 | 0.105 | 39.79 | 3.255 | 72.64
110 | -0.81 | 0 | 0.11 | 40.73 | 3.25 | 71.94
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
