bluepylons/Open-Switch-Curve-Meter/Force curves/April-10-21-calibration/Gazzew-U4-stem-in-Cherry-MX-Clear.ods

Raw data |  |  | Corrected Downstroke |  | Corrected Upstroke
X (microns) | Force (gf) | Actuated? | X (mm) | Force (gf) | X (mm) | Force (gf)
0 | -0.75 | 0 | 0 | 0.3 | 3.32 | 109.63
5 | -0.74 | 0 | 0.005 | 3.92 | 3.315 | 106.2
10 | -0.73 | 0 | 0.01 | 8.6 | 3.31 | 104.49
15 | -0.75 | 0 | 0.015 | 10.2 | 3.305 | 101.63
20 | -0.76 | 0 | 0.02 | 14.09 | 3.3 | 100.13
25 | -0.74 | 0 | 0.025 | 15.99 | 3.295 | 98.81
30 | -0.73 | 0 | 0.03 | 17.7 | 3.29 | 95.99
35 | -0.75 | 0 | 0.035 | 20.55 | 3.285 | 94.63
40 | -0.77 | 0 | 0.04 | 21.97 | 3.28 | 91.94
45 | -0.77 | 0 | 0.045 | 24.61 | 3.275 | 90.68
50 | -0.73 | 0 | 0.05 | 26.01 | 3.27 | 87.99
55 | -0.73 | 0 | 0.055 | 28.4 | 3.265 | 86.66
60 | -0.77 | 0 | 0.06 | 29.63 | 3.26 | 85.37
65 | -0.75 | 0 | 0.065 | 30.76 | 3.255 | 82.87
70 | -0.76 | 0 | 0.07 | 33.01 | 3.25 | 81.6
75 | -0.77 | 0 | 0.075 | 34.05 | 3.245 | 79.25
80 | -0.73 | 0 | 0.08 | 36.22 | 3.24 | 78.07
85 | -0.74 | 0 | 0.085 | 37.29 | 3.235 | 75.98
90 | -0.72 | 0 | 0.09 | 39.11 | 3.23 | 74.94
95 | -0.73 | 0 | 0.095 | 39.77 | 3.225 | 74.05
100 | -0.74 | 0 | 0.1 | 40.47 | 3.22 | 72.24
105 | -0.75 | 0 | 0.105 | 41.68 | 3.215 | 71.32
110 | -0.79 | 0 | 0.11 | 42.12 | 3.21 | 69.48
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
