bluepylons/Open-Switch-Curve-Meter/Force curves/April-10-21-calibration/JWK-Alpaca-V2.ods

Raw data |  |  | Corrected Downstroke |  | Corrected Upstroke
X (microns) | Force (gf) | Actuated? | X (mm) | Force (gf) | X (mm) | Force (gf)
0 | -0.09 | 0 | 0 | 0.51 | 3.95 | 63.62
5 | -0.09 | 0 | 0.005 | 5.77 | 3.945 | 59
10 | -0.07 | 0 | 0.01 | 23.85 | 3.94 | 57.83
15 | -0.08 | 0 | 0.015 | 27.56 | 3.935 | 57.07
20 | -0.06 | 0 | 0.02 | 28.69 | 3.93 | 56.91
25 | -0.07 | 0 | 0.025 | 28.45 | 3.925 | 56.65
30 | -0.07 | 0 | 0.03 | 28.3 | 3.92 | 56.58
35 | -0.08 | 0 | 0.035 | 28.21 | 3.915 | 56.54
40 | -0.09 | 0 | 0.04 | 28.2 | 3.91 | 56.48
45 | -0.07 | 0 | 0.045 | 28.06 | 3.905 | 56.45
50 | -0.1 | 0 | 0.05 | 28.06 | 3.9 | 56.47
55 | -0.09 | 0 | 0.055 | 27.97 | 3.895 | 56.48
60 | -0.07 | 0 | 0.06 | 27.96 | 3.89 | 56.46
65 | -0.06 | 0 | 0.065 | 27.9 | 3.885 | 56.49
70 | -0.09 | 0 | 0.07 | 27.85 | 3.88 | 56.5
75 | -0.1 | 0 | 0.075 | 27.79 | 3.875 | 56.47
80 | -0.08 | 0 | 0.08 | 27.72 | 3.87 | 56.4
85 | -0.07 | 0 | 0.085 | 27.67 | 3.865 | 56.29
90 | -0.09 | 0 | 0.09 | 27.59 | 3.86 | 56.21
95 | -0.06 | 0 | 0.095 | 27.58 | 3.855 | 56.08
100 | -0.06 | 0 | 0.1 | 27.65 | 3.85 | 56.02
105 | -0.07 | 0 | 0.105 | 27.59 | 3.845 | 55.97
110 | -0.08 | 0 | 0.11 | 27.69 | 3.84 | 55.93
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
