bluepylons/Open-Switch-Curve-Meter/Force curves/April-10-21-calibration/Kailh-Box-Navy.ods

Raw data |  |  | Corrected Downstroke |  | Corrected Upstroke
X (microns) | Force (gf) | Actuated? | X (mm) | Force (gf) | X (mm) | Force (gf)
0 | -0.82 | 0 | 0 | 4.71 | 3.715 | 86.8
5 | -0.81 | 0 | 0.005 | 20.57 | 3.71 | 86.7
10 | -0.74 | 0 | 0.01 | 28.93 | 3.705 | 86.67
15 | -0.78 | 0 | 0.015 | 38.82 | 3.7 | 86.55
20 | -0.78 | 0 | 0.02 | 37.99 | 3.695 | 86.51
25 | -0.76 | 0 | 0.025 | 36.75 | 3.69 | 86.43
30 | -0.76 | 0 | 0.03 | 36.71 | 3.685 | 86.37
35 | -0.83 | 0 | 0.035 | 37.21 | 3.68 | 86.3
40 | -0.8 | 0 | 0.04 | 38.55 | 3.675 | 86.29
45 | -0.79 | 0 | 0.045 | 41.22 | 3.67 | 86.27
50 | -0.83 | 0 | 0.05 | 45.93 | 3.665 | 86.15
55 | -0.85 | 0 | 0.055 | 47.29 | 3.66 | 86.1
60 | -0.8 | 0 | 0.06 | 48.5 | 3.655 | 86.02
65 | -0.82 | 0 | 0.065 | 50.31 | 3.65 | 85.98
70 | -0.79 | 0 | 0.07 | 50.64 | 3.645 | 85.96
75 | -0.8 | 0 | 0.075 | 50.79 | 3.64 | 85.92
80 | -0.81 | 0 | 0.08 | 50.86 | 3.635 | 85.87
85 | -0.79 | 0 | 0.085 | 51.04 | 3.63 | 85.76
90 | -0.79 | 0 | 0.09 | 51.13 | 3.625 | 85.72
95 | -0.83 | 0 | 0.095 | 51.21 | 3.62 | 85.67
100 | -0.85 | 0 | 0.1 | 51.43 | 3.615 | 85.63
105 | -0.8 | 0 | 0.105 | 51.6 | 3.61 | 85.59
110 | -0.79 | 0 | 0.11 | 52.01 | 3.605 | 85.48
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
