bluepylons/Open-Switch-Curve-Meter/Force curves/April-10-21-calibration/Kailh-Pro-Burgundy-stem-In-Gateron-KS-3-bottom-Gazzew-Boba-top.ods

Raw data |  |  | Corrected Downstroke |  | Corrected Upstroke
X (microns) | Force (gf) | Actuated? | X (mm) | Force (gf) | X (mm) | Force (gf)
0 | -0.23 | 0 | 0 | 2.94 | 2.95 | 55.83
5 | -0.25 | 0 | 0.005 | 9.21 | 2.945 | 55.75
10 | -0.24 | 0 | 0.01 | 22.93 | 2.94 | 55.8
15 | -0.23 | 0 | 0.015 | 29.84 | 2.935 | 55.58
20 | -0.24 | 0 | 0.02 | 34.97 | 2.93 | 55.52
25 | -0.21 | 0 | 0.025 | 34.12 | 2.925 | 55.39
30 | -0.23 | 0 | 0.03 | 32.92 | 2.92 | 55.44
35 | -0.22 | 0 | 0.035 | 32.62 | 2.915 | 55.35
40 | -0.23 | 0 | 0.04 | 32.11 | 2.91 | 55.36
45 | -0.21 | 0 | 0.045 | 31.65 | 2.905 | 55.29
50 | -0.22 | 0 | 0.05 | 31.49 | 2.9 | 55.3
55 | -0.23 | 0 | 0.055 | 31.27 | 2.895 | 55.27
60 | -0.23 | 0 | 0.06 | 31.21 | 2.89 | 55.29
65 | -0.24 | 0 | 0.065 | 30.98 | 2.885 | 55.22
70 | -0.22 | 0 | 0.07 | 31.01 | 2.88 | 55.12
75 | -0.22 | 0 | 0.075 | 30.95 | 2.875 | 54.99
80 | -0.22 | 0 | 0.08 | 31.03 | 2.87 | 54.86
85 | -0.21 | 0 | 0.085 | 31.06 | 2.865 | 54.85
90 | -0.21 | 0 | 0.09 | 31.25 | 2.86 | 55.05
95 | -0.2 | 0 | 0.095 | 31.55 | 2.855 | 55.02
100 | -0.22 | 0 | 0.1 | 31.74 | 2.85 | 54.97
105 | -0.25 | 0 | 0.105 | 31.89 | 2.845 | 54.9
110 | -0.21 | 0 | 0.11 | 31.89 | 2.84 | 54.95
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
