bluepylons/Open-Switch-Curve-Meter/Force curves/April-10-21-calibration/Kailh-Pro-Purple-Stem-In-T1-Bottom-Boba-Top.ods

Raw data |  |  | Corrected Downstroke |  | Corrected Upstroke
X (microns) | Force (gf) | Actuated? | X (mm) | Force (gf) | X (mm) | Force (gf)
0 | 0.02 | 0 | 0 | 9.08 | 2.815 | 54.69
5 | 0.04 | 0 | 0.005 | 17.75 | 2.81 | 54.88
10 | 0.06 | 0 | 0.01 | 34.43 | 2.805 | 54.86
15 | 0.05 | 0 | 0.015 | 38.78 | 2.8 | 54.99
20 | 0.04 | 0 | 0.02 | 40.63 | 2.795 | 54.87
25 | 0.05 | 0 | 0.025 | 42 | 2.79 | 54.97
30 | 0.02 | 0 | 0.03 | 41.84 | 2.785 | 54.89
35 | 0.04 | 0 | 0.035 | 41.24 | 2.78 | 54.76
40 | 0.05 | 0 | 0.04 | 41.1 | 2.775 | 54.53
45 | 0.02 | 0 | 0.045 | 40.98 | 2.77 | 54.42
50 | 0.03 | 0 | 0.05 | 40.91 | 2.765 | 54.33
55 | 0.02 | 0 | 0.055 | 40.84 | 2.76 | 54.51
60 | 0.06 | 0 | 0.06 | 41.41 | 2.755 | 54.39
65 | 0.06 | 0 | 0.065 | 42.38 | 2.75 | 54.4
70 | 0.03 | 0 | 0.07 | 44.06 | 2.745 | 54.28
75 | 0.05 | 0 | 0.075 | 44.61 | 2.74 | 54.27
80 | 0.04 | 0 | 0.08 | 44.98 | 2.735 | 54.04
85 | 0.05 | 0 | 0.085 | 45.13 | 2.73 | 54.15
90 | 0.07 | 0 | 0.09 | 45.25 | 2.725 | 53.96
95 | 0.04 | 0 | 0.095 | 45.44 | 2.72 | 54.05
100 | 0.04 | 0 | 0.1 | 45.38 | 2.715 | 53.87
105 | 0.03 | 0 | 0.105 | 45.5 | 2.71 | 53.86
110 | 0.03 | 0 | 0.11 | 45.53 | 2.705 | 53.81
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
