bluepylons/Open-Switch-Curve-Meter/Force curves/April-10-21-calibration/Kailh-Pro-Purple-Stem-In-T1-Bottom-Cherry-Top.ods

Raw data |  |  | Corrected Downstroke |  | Corrected Upstroke
X (microns) | Force (gf) | Actuated? | X (mm) | Force (gf) | X (mm) | Force (gf)
0 | -0.51 | 0 | 0 | 7.25 | 3.155 | 57.01
5 | -0.47 | 0 | 0.005 | 16.49 | 3.15 | 55.84
10 | -0.48 | 0 | 0.01 | 21.57 | 3.145 | 55.77
15 | -0.48 | 0 | 0.015 | 24.81 | 3.14 | 55.74
20 | -0.47 | 0 | 0.02 | 26.46 | 3.135 | 55.66
25 | -0.49 | 0 | 0.025 | 27.5 | 3.13 | 55.61
30 | -0.47 | 0 | 0.03 | 27.37 | 3.125 | 55.61
35 | -0.51 | 0 | 0.035 | 27.32 | 3.12 | 55.57
40 | -0.51 | 0 | 0.04 | 27.9 | 3.115 | 55.55
45 | -0.48 | 0 | 0.045 | 28.19 | 3.11 | 55.54
50 | -0.49 | 0 | 0.05 | 28.17 | 3.105 | 55.49
55 | -0.5 | 0 | 0.055 | 28.22 | 3.1 | 55.39
60 | -0.48 | 0 | 0.06 | 28.97 | 3.095 | 55.34
65 | -0.5 | 0 | 0.065 | 29.42 | 3.09 | 55.3
70 | -0.47 | 0 | 0.07 | 29.37 | 3.085 | 55.28
75 | -0.46 | 0 | 0.075 | 29.15 | 3.08 | 55.2
80 | -0.48 | 0 | 0.08 | 29.41 | 3.075 | 55.15
85 | -0.45 | 0 | 0.085 | 30.88 | 3.07 | 55.12
90 | -0.43 | 0 | 0.09 | 31.75 | 3.065 | 55.08
95 | -0.5 | 0 | 0.095 | 33.11 | 3.06 | 55.05
100 | -0.49 | 0 | 0.1 | 33.25 | 3.055 | 54.93
105 | -0.48 | 0 | 0.105 | 33.13 | 3.05 | 54.93
110 | -0.47 | 0 | 0.11 | 33.12 | 3.045 | 54.86
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
