bluepylons/Open-Switch-Curve-Meter/Force curves/April-10-21-calibration/Kailh-Pro-Purple-Stem-In-T1-Bottom-Gateron-Milky-Top.ods

Raw data |  |  | Corrected Downstroke |  | Corrected Upstroke
X (microns) | Force (gf) | Actuated? | X (mm) | Force (gf) | X (mm) | Force (gf)
0 | -0.59 | 0 | 0 | 11.33 | 3.205 | 87.38
5 | -0.58 | 0 | 0.005 | 19.44 | 3.2 | 71.07
10 | -0.57 | 0 | 0.01 | 28.98 | 3.195 | 63.66
15 | -0.57 | 0 | 0.015 | 29.94 | 3.19 | 58.61
20 | -0.57 | 0 | 0.02 | 30.92 | 3.185 | 55.7
25 | -0.57 | 0 | 0.025 | 32.4 | 3.18 | 55.68
30 | -0.57 | 0 | 0.03 | 32.02 | 3.175 | 55.63
35 | -0.58 | 0 | 0.035 | 27.11 | 3.17 | 55.62
40 | -0.57 | 0 | 0.04 | 28.52 | 3.165 | 55.59
45 | -0.57 | 0 | 0.045 | 28.94 | 3.16 | 55.55
50 | -0.58 | 0 | 0.05 | 29.82 | 3.155 | 55.52
55 | -0.6 | 0 | 0.055 | 30.7 | 3.15 | 55.46
60 | -0.57 | 0 | 0.06 | 31.46 | 3.145 | 55.4
65 | -0.58 | 0 | 0.065 | 31.56 | 3.14 | 55.23
70 | -0.56 | 0 | 0.07 | 31.47 | 3.135 | 55.12
75 | -0.56 | 0 | 0.075 | 31.38 | 3.13 | 55.03
80 | -0.53 | 0 | 0.08 | 31.53 | 3.125 | 54.97
85 | -0.55 | 0 | 0.085 | 31.69 | 3.12 | 54.93
90 | -0.55 | 0 | 0.09 | 31.84 | 3.115 | 54.95
95 | -0.61 | 0 | 0.095 | 31.98 | 3.11 | 54.96
100 | -0.61 | 0 | 0.1 | 32.03 | 3.105 | 54.92
105 | -0.58 | 0 | 0.105 | 31.99 | 3.1 | 54.85
110 | -0.59 | 0 | 0.11 | 32.06 | 3.095 | 54.83
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
