bluepylons/Open-Switch-Curve-Meter/Force curves/April-10-21-calibration/Kailh-Pro-Purple-Stem-In-T1-Bottom-Outemu-Clear-No-Slot-Top.ods

Raw data |  |  | Corrected Downstroke |  | Corrected Upstroke
X (microns) | Force (gf) | Actuated? | X (mm) | Force (gf) | X (mm) | Force (gf)
0 | -0.36 | 0 | 0 | 4.69 | 2.86 | 55.68
5 | -0.36 | 0 | 0.005 | 12.61 | 2.855 | 55.63
10 | -0.36 | 0 | 0.01 | 28.72 | 2.85 | 55.51
15 | -0.34 | 0 | 0.015 | 32.21 | 2.845 | 55.45
20 | -0.34 | 0 | 0.02 | 33.92 | 2.84 | 55.44
25 | -0.37 | 0 | 0.025 | 35.05 | 2.835 | 55.39
30 | -0.39 | 0 | 0.03 | 35.24 | 2.83 | 55.35
35 | -0.37 | 0 | 0.035 | 35.76 | 2.825 | 55.23
40 | -0.35 | 0 | 0.04 | 36.73 | 2.82 | 55.17
45 | -0.33 | 0 | 0.045 | 38.75 | 2.815 | 55
50 | -0.33 | 0 | 0.05 | 39.7 | 2.81 | 54.92
55 | -0.35 | 0 | 0.055 | 40.72 | 2.805 | 54.91
60 | -0.36 | 0 | 0.06 | 42.38 | 2.8 | 54.94
65 | -0.37 | 0 | 0.065 | 42.67 | 2.795 | 54.82
70 | -0.35 | 0 | 0.07 | 42.8 | 2.79 | 54.76
75 | -0.33 | 0 | 0.075 | 42.64 | 2.785 | 54.63
80 | -0.32 | 0 | 0.08 | 42.57 | 2.78 | 54.63
85 | -0.36 | 0 | 0.085 | 42.46 | 2.775 | 54.52
90 | -0.37 | 0 | 0.09 | 42.4 | 2.77 | 54.48
95 | -0.43 | 0 | 0.095 | 42.47 | 2.765 | 54.38
100 | -0.4 | 0 | 0.1 | 42.82 | 2.76 | 54.38
105 | -0.39 | 0 | 0.105 | 43.01 | 2.755 | 54.25
110 | -0.34 | 0 | 0.11 | 42.92 | 2.75 | 54.24
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
