bluepylons/Open-Switch-Curve-Meter/Force curves/April-10-21-calibration/Kailh-Pro-Purple-Stem-In-T1-Bottom-Outemu-Clear-Slotted-Top.ods

Raw data |  |  | Corrected Downstroke |  | Corrected Upstroke
X (microns) | Force (gf) | Actuated? | X (mm) | Force (gf) | X (mm) | Force (gf)
0 | -0.39 | 0 | 0 | 0.53 | 2.875 | 55.4
5 | -0.4 | 0 | 0.005 | 13.06 | 2.87 | 55.36
10 | -0.41 | 0 | 0.01 | 22.7 | 2.865 | 55.31
15 | -0.42 | 0 | 0.015 | 37.36 | 2.86 | 55.25
20 | -0.4 | 0 | 0.02 | 39.74 | 2.855 | 55.21
25 | -0.43 | 0 | 0.025 | 40.95 | 2.85 | 55.2
30 | -0.43 | 0 | 0.03 | 42.03 | 2.845 | 55.15
35 | -0.42 | 0 | 0.035 | 42.17 | 2.84 | 55.12
40 | -0.43 | 0 | 0.04 | 42.21 | 2.835 | 55.19
45 | -0.4 | 0 | 0.045 | 41.83 | 2.83 | 55.14
50 | -0.42 | 0 | 0.05 | 41.15 | 2.825 | 55.11
55 | -0.42 | 0 | 0.055 | 41.02 | 2.82 | 55.07
60 | -0.41 | 0 | 0.06 | 41.09 | 2.815 | 55.07
65 | -0.38 | 0 | 0.065 | 40.99 | 2.81 | 54.86
70 | -0.42 | 0 | 0.07 | 40.73 | 2.805 | 54.71
75 | -0.42 | 0 | 0.075 | 40.5 | 2.8 | 54.67
80 | -0.38 | 0 | 0.08 | 40.81 | 2.795 | 54.68
85 | -0.41 | 0 | 0.085 | 40.89 | 2.79 | 54.63
90 | -0.41 | 0 | 0.09 | 40.99 | 2.785 | 54.53
95 | -0.36 | 0 | 0.095 | 41.11 | 2.78 | 54.47
100 | -0.41 | 0 | 0.1 | 41.68 | 2.775 | 54.37
105 | -0.44 | 0 | 0.105 | 41.88 | 2.77 | 54.34
110 | -0.43 | 0 | 0.11 | 42.02 | 2.765 | 54.22
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
