bluepylons/Open-Switch-Curve-Meter/Force curves/April-10-21-calibration/Kailh-Pro-Purple-Stem-In-T1.ods

Raw data |  |  | Corrected Downstroke |  | Corrected Upstroke
X (microns) | Force (gf) | Actuated? | X (mm) | Force (gf) | X (mm) | Force (gf)
0 | -0.04 | 0 | 0 | 0.07 | 3.105 | 81.96
5 | -0.06 | 0 | 0.005 | 2.02 | 3.1 | 73.55
10 | -0.07 | 0 | 0.01 | 14.79 | 3.095 | 59
15 | -0.06 | 0 | 0.015 | 21.79 | 3.09 | 56.52
20 | -0.07 | 0 | 0.02 | 27.33 | 3.085 | 56.1
25 | -0.09 | 0 | 0.025 | 28.23 | 3.08 | 56.07
30 | -0.06 | 0 | 0.03 | 29.86 | 3.075 | 55.99
35 | -0.04 | 0 | 0.035 | 30.63 | 3.07 | 55.96
40 | -0.04 | 0 | 0.04 | 30.84 | 3.065 | 55.97
45 | -0.06 | 0 | 0.045 | 31.49 | 3.06 | 55.82
50 | -0.06 | 0 | 0.05 | 32.36 | 3.055 | 55.78
55 | -0.08 | 0 | 0.055 | 34.02 | 3.05 | 55.7
60 | -0.02 | 0 | 0.06 | 33.99 | 3.045 | 55.69
65 | -0.04 | 0 | 0.065 | 33.71 | 3.04 | 55.63
70 | -0.07 | 0 | 0.07 | 33.58 | 3.035 | 55.56
75 | 0.07 | 0 | 0.075 | 33.51 | 3.03 | 55.52
80 | 2.02 | 0 | 0.08 | 33.4 | 3.025 | 55.49
85 | 14.79 | 0 | 0.085 | 33.37 | 3.02 | 55.46
90 | 21.79 | 0 | 0.09 | 33.26 | 3.015 | 55.42
95 | 27.33 | 0 | 0.095 | 33.3 | 3.01 | 55.37
100 | 28.23 | 0 | 0.1 | 33.44 | 3.005 | 55.37
105 | 29.86 | 0 | 0.105 | 33.4 | 3 | 55.35
110 | 30.63 | 0 | 0.11 | 33.34 | 2.995 | 55.3
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
