bluepylons/Open-Switch-Curve-Meter/Force curves/April-10-21-calibration/Kailh-Speed-Navy.ods

Raw data |  |  | Corrected Downstroke |  | Corrected Upstroke
X (microns) | Force (gf) | Actuated? | X (mm) | Force (gf) | X (mm) | Force (gf)
0 | -0.07 | 0 | 0 | 1.79 | 3.54 | 103.82
5 | -0.08 | 0 | 0.005 | 9.58 | 3.535 | 96.27
10 | -0.09 | 0 | 0.01 | 28.17 | 3.53 | 95.09
15 | -0.09 | 0 | 0.015 | 35.67 | 3.525 | 94.53
20 | -0.08 | 0 | 0.02 | 43.47 | 3.52 | 94.45
25 | -0.09 | 0 | 0.025 | 44.71 | 3.515 | 94.36
30 | -0.07 | 0 | 0.03 | 46.25 | 3.51 | 94.36
35 | -0.08 | 0 | 0.035 | 46.95 | 3.505 | 94.32
40 | -0.1 | 0 | 0.04 | 48.24 | 3.5 | 94.2
45 | -0.1 | 0 | 0.045 | 48.54 | 3.495 | 94.14
50 | -0.12 | 0 | 0.05 | 48.46 | 3.49 | 93.97
55 | -0.08 | 0 | 0.055 | 48.2 | 3.485 | 93.92
60 | -0.08 | 0 | 0.06 | 47.95 | 3.48 | 93.87
65 | -0.07 | 0 | 0.065 | 47.93 | 3.475 | 93.88
70 | -0.08 | 0 | 0.07 | 47.98 | 3.47 | 93.81
75 | -0.1 | 0 | 0.075 | 48.09 | 3.465 | 93.76
80 | -0.09 | 0 | 0.08 | 48.09 | 3.46 | 93.63
85 | -0.1 | 0 | 0.085 | 47.95 | 3.455 | 93.6
90 | -0.07 | 0 | 0.09 | 47.93 | 3.45 | 93.56
95 | -0.07 | 0 | 0.095 | 47.85 | 3.445 | 93.54
100 | -0.12 | 0 | 0.1 | 47.92 | 3.44 | 93.4
105 | -0.1 | 0 | 0.105 | 48 | 3.435 | 93.33
110 | -0.09 | 0 | 0.11 | 47.97 | 3.43 | 93.29
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
