bluepylons/Open-Switch-Curve-Meter/Force curves/April-10-21-calibration/Kailh-Speed-Pale-Blue-Stem-In-NK-Sherbet-housing.ods

Raw data |  |  | Corrected Downstroke |  | Corrected Upstroke
X (microns) | Force (gf) | Actuated? | X (mm) | Force (gf) | X (mm) | Force (gf)
0 | -0.27 | 0 | 0 | 3.93 | 3.47 | 85.96
5 | -0.28 | 0 | 0.005 | 12.25 | 3.465 | 83.38
10 | -0.25 | 0 | 0.01 | 27.62 | 3.46 | 82.15
15 | -0.24 | 0 | 0.015 | 30.9 | 3.455 | 82.11
20 | -0.22 | 0 | 0.02 | 33.58 | 3.45 | 82.04
25 | -0.22 | 0 | 0.025 | 34.14 | 3.445 | 81.95
30 | -0.23 | 0 | 0.03 | 34.24 | 3.44 | 81.86
35 | -0.24 | 0 | 0.035 | 34.22 | 3.435 | 81.74
40 | -0.24 | 0 | 0.04 | 34.26 | 3.43 | 81.69
45 | -0.23 | 0 | 0.045 | 34.34 | 3.425 | 81.65
50 | -0.26 | 0 | 0.05 | 34.47 | 3.42 | 81.62
55 | -0.28 | 0 | 0.055 | 34.72 | 3.415 | 81.5
60 | -0.28 | 0 | 0.06 | 35.11 | 3.41 | 81.49
65 | -0.25 | 0 | 0.065 | 35.28 | 3.405 | 81.49
70 | -0.27 | 0 | 0.07 | 35.58 | 3.4 | 81.44
75 | -0.29 | 0 | 0.075 | 36.2 | 3.395 | 81.32
80 | -0.26 | 0 | 0.08 | 36.3 | 3.39 | 81.27
85 | -0.24 | 0 | 0.085 | 36.4 | 3.385 | 81.23
90 | -0.3 | 0 | 0.09 | 36.44 | 3.38 | 81.22
95 | -0.29 | 0 | 0.095 | 36.8 | 3.375 | 81.16
100 | -0.29 | 0 | 0.1 | 36.68 | 3.37 | 81.01
105 | -0.27 | 0 | 0.105 | 36.5 | 3.365 | 80.98
110 | -0.28 | 0 | 0.11 | 36.39 | 3.36 | 81.04
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
