bluepylons/Open-Switch-Curve-Meter/Force curves/April-10-21-calibration/MX-Brown-Stem-In-Boba-Housing.ods

Raw data |  |  | Corrected Downstroke |  | Corrected Upstroke
X (microns) | Force (gf) | Actuated? | X (mm) | Force (gf) | X (mm) | Force (gf)
0 | -0.34 | 0 | 0 | 3.16 | 3.805 | 66.33
5 | -0.33 | 0 | 0.005 | 11.43 | 3.8 | 66.25
10 | -0.34 | 0 | 0.01 | 28.25 | 3.795 | 66.19
15 | -0.34 | 0 | 0.015 | 32.73 | 3.79 | 66.09
20 | -0.34 | 0 | 0.02 | 35.99 | 3.785 | 66.1
25 | -0.37 | 0 | 0.025 | 38.67 | 3.78 | 66.11
30 | -0.33 | 0 | 0.03 | 40.39 | 3.775 | 66.14
35 | -0.35 | 0 | 0.035 | 41.33 | 3.77 | 66.16
40 | -0.35 | 0 | 0.04 | 41.43 | 3.765 | 66.15
45 | -0.35 | 0 | 0.045 | 41.58 | 3.76 | 66.16
50 | -0.35 | 0 | 0.05 | 41.58 | 3.755 | 66.15
55 | -0.33 | 0 | 0.055 | 41.24 | 3.75 | 66.06
60 | -0.35 | 0 | 0.06 | 40.23 | 3.745 | 65.96
65 | -0.35 | 0 | 0.065 | 39.46 | 3.74 | 65.86
70 | -0.34 | 0 | 0.07 | 38.49 | 3.735 | 65.84
75 | -0.36 | 0 | 0.075 | 37.59 | 3.73 | 65.75
80 | -0.33 | 0 | 0.08 | 37.11 | 3.725 | 65.72
85 | -0.33 | 0 | 0.085 | 37.05 | 3.72 | 65.63
90 | -0.33 | 0 | 0.09 | 37.06 | 3.715 | 65.54
95 | -0.35 | 0 | 0.095 | 37 | 3.71 | 65.46
100 | -0.37 | 0 | 0.1 | 36.95 | 3.705 | 65.42
105 | -0.31 | 0 | 0.105 | 36.95 | 3.7 | 65.39
110 | -0.32 | 0 | 0.11 | 37.04 | 3.695 | 65.29
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
