bluepylons/Open-Switch-Curve-Meter/Force curves/April-10-21-calibration/NK-Cream-stem-in-Alpaca-V2.ods

Raw data |  |  | Corrected Downstroke |  | Corrected Upstroke
X (microns) | Force (gf) | Actuated? | X (mm) | Force (gf) | X (mm) | Force (gf)
0 | -0.16 | 0 | 0 | 0.46 | 3.225 | 64.4
5 | -0.16 | 0 | 0.005 | 3.86 | 3.22 | 56.72
10 | -0.18 | 0 | 0.01 | 10.52 | 3.215 | 51.5
15 | -0.19 | 0 | 0.015 | 24.28 | 3.21 | 49.34
20 | -0.15 | 0 | 0.02 | 26.96 | 3.205 | 49.89
25 | -0.19 | 0 | 0.025 | 28.84 | 3.2 | 50.02
30 | -0.18 | 0 | 0.03 | 29.25 | 3.195 | 50.09
35 | -0.18 | 0 | 0.035 | 30.24 | 3.19 | 49.9
40 | -0.12 | 0 | 0.04 | 30.57 | 3.185 | 50.05
45 | -0.16 | 0 | 0.045 | 30.74 | 3.18 | 50.05
50 | -0.11 | 0 | 0.05 | 30.58 | 3.175 | 50.05
55 | -0.16 | 0 | 0.055 | 30.48 | 3.17 | 49.94
60 | -0.12 | 0 | 0.06 | 29.97 | 3.165 | 49.88
65 | -0.17 | 0 | 0.065 | 29.86 | 3.16 | 49.84
70 | -0.22 | 0 | 0.07 | 29.49 | 3.155 | 49.9
75 | -0.2 | 0 | 0.075 | 29.51 | 3.15 | 49.76
80 | -0.08 | 0 | 0.08 | 29.45 | 3.145 | 49.7
85 | -0.12 | 0 | 0.085 | 29.42 | 3.14 | 49.62
90 | -0.22 | 0 | 0.09 | 29.38 | 3.135 | 49.63
95 | -0.23 | 0 | 0.095 | 29.47 | 3.13 | 49.46
100 | -0.11 | 0 | 0.1 | 29.5 | 3.125 | 49.51
105 | -0.14 | 0 | 0.105 | 29.57 | 3.12 | 49.38
110 | -0.19 | 0 | 0.11 | 29.6 | 3.115 | 49.49
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
