bluepylons/Open-Switch-Curve-Meter/Force curves/April-10-21-calibration/Outemu Ice Purple.ods

Raw data |  |  | Corrected Downstroke |  | Corrected Upstroke
X (microns) | Force (gf) | Actuated? | X (mm) | Force (gf) | X (mm) | Force (gf)
0 | -0.38 | 0 | 0 | 2.51 | 3.745 | 64.77
5 | -0.39 | 0 | 0.005 | 11.27 | 3.74 | 64.42
10 | -0.37 | 0 | 0.01 | 28.81 | 3.735 | 64.3
15 | -0.38 | 0 | 0.015 | 33.61 | 3.73 | 64.12
20 | -0.38 | 0 | 0.02 | 34.57 | 3.725 | 64
25 | -0.35 | 0 | 0.025 | 35.61 | 3.72 | 63.89
30 | -0.33 | 0 | 0.03 | 36.69 | 3.715 | 63.77
35 | -0.34 | 0 | 0.035 | 36.43 | 3.71 | 63.63
40 | -0.37 | 0 | 0.04 | 35.73 | 3.705 | 63.45
45 | -0.34 | 0 | 0.045 | 35.5 | 3.7 | 63.39
50 | -0.35 | 0 | 0.05 | 35.31 | 3.695 | 63.16
55 | -0.36 | 0 | 0.055 | 35.52 | 3.69 | 63.13
60 | -0.33 | 0 | 0.06 | 35.51 | 3.685 | 63.03
65 | -0.33 | 0 | 0.065 | 35.5 | 3.68 | 63
70 | -0.33 | 0 | 0.07 | 35.49 | 3.675 | 62.89
75 | -0.3 | 0 | 0.075 | 35.67 | 3.67 | 62.91
80 | 2.51 | 0 | 0.08 | 35.66 | 3.665 | 62.92
85 | 11.27 | 0 | 0.085 | 35.62 | 3.66 | 62.86
90 | 28.81 | 0 | 0.09 | 35.6 | 3.655 | 62.68
95 | 33.61 | 0 | 0.095 | 35.79 | 3.65 | 62.65
100 | 34.57 | 0 | 0.1 | 35.82 | 3.645 | 62.63
105 | 35.61 | 0 | 0.105 | 35.87 | 3.64 | 62.63
110 | 36.69 | 0 | 0.11 | 35.86 | 3.635 | 62.57
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
