bluepylons/Open-Switch-Curve-Meter/Force curves/April-10-21-calibration/Outemu-Purple-Dustproof-In-Boba.ods

Raw data |  |  | Corrected Downstroke |  | Corrected Upstroke
X (microns) | Force (gf) | Actuated? | X (mm) | Force (gf) | X (mm) | Force (gf)
0 | -0.64 | 0 | 0 | 7.88 | 3.85 | 61.34
5 | -0.67 | 0 | 0.005 | 12.75 | 3.845 | 61.27
10 | -0.69 | 0 | 0.01 | 17.07 | 3.84 | 61.27
15 | -0.67 | 0 | 0.015 | 24.79 | 3.835 | 61.25
20 | -0.66 | 0 | 0.02 | 27.08 | 3.83 | 61.21
25 | -0.66 | 0 | 0.025 | 28.64 | 3.825 | 61.14
30 | -0.66 | 0 | 0.03 | 28.98 | 3.82 | 60.99
35 | -0.67 | 0 | 0.035 | 28.67 | 3.815 | 60.91
40 | -0.64 | 0 | 0.04 | 28.82 | 3.81 | 60.86
45 | -0.68 | 0 | 0.045 | 29.49 | 3.805 | 60.76
50 | -0.67 | 0 | 0.05 | 32.14 | 3.8 | 60.71
55 | -0.68 | 0 | 0.055 | 33.32 | 3.795 | 60.65
60 | -0.67 | 0 | 0.06 | 35.01 | 3.79 | 60.6
65 | -0.64 | 0 | 0.065 | 35.58 | 3.785 | 60.55
70 | -0.69 | 0 | 0.07 | 36.96 | 3.78 | 60.5
75 | -0.7 | 0 | 0.075 | 36.57 | 3.775 | 60.46
80 | -0.67 | 0 | 0.08 | 36.08 | 3.77 | 60.44
85 | -0.67 | 0 | 0.085 | 35.25 | 3.765 | 60.43
90 | -0.67 | 0 | 0.09 | 35.43 | 3.76 | 60.36
95 | -0.66 | 0 | 0.095 | 35.56 | 3.755 | 60.32
100 | -0.67 | 0 | 0.1 | 35.46 | 3.75 | 60.26
105 | -0.66 | 0 | 0.105 | 35.15 | 3.745 | 60.2
110 | -0.66 | 0 | 0.11 | 35.5 | 3.74 | 60.15
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
