bluepylons/Open-Switch-Curve-Meter/Force curves/April-10-21-calibration/Outemu-Silent-Sky-Stem-in-Cherry-MX-Blue-housing.ods

Raw data |  |  | Corrected Downstroke |  | Corrected Upstroke
X (microns) | Force (gf) | Actuated? | X (mm) | Force (gf) | X (mm) | Force (gf)
0 | -0.81 | 0 | 0 | 6.56 | 3.285 | 107.15
5 | -0.81 | 0 | 0.005 | 9.54 | 3.28 | 104.32
10 | -0.8 | 0 | 0.01 | 12.88 | 3.275 | 103.05
15 | -0.8 | 0 | 0.015 | 14.64 | 3.27 | 100.4
20 | -0.79 | 0 | 0.02 | 16.49 | 3.265 | 99.17
25 | -0.8 | 0 | 0.025 | 19.99 | 3.26 | 96.55
30 | -0.82 | 0 | 0.03 | 21.13 | 3.255 | 95.36
35 | -0.8 | 0 | 0.035 | 22.65 | 3.25 | 94.11
40 | -0.8 | 0 | 0.04 | 23.58 | 3.245 | 91.74
45 | -0.8 | 0 | 0.045 | 25.32 | 3.24 | 90.49
50 | -0.8 | 0 | 0.05 | 26.15 | 3.235 | 88.27
55 | -0.78 | 0 | 0.055 | 26.87 | 3.23 | 87.22
60 | -0.78 | 0 | 0.06 | 27.78 | 3.225 | 85.34
65 | -0.82 | 0 | 0.065 | 28.25 | 3.22 | 84.28
70 | -0.79 | 0 | 0.07 | 29.21 | 3.215 | 83.24
75 | -0.81 | 0 | 0.075 | 29.55 | 3.21 | 81.13
80 | -0.8 | 0 | 0.08 | 30.08 | 3.205 | 80.15
85 | -0.81 | 0 | 0.085 | 30.5 | 3.2 | 78.24
90 | -0.83 | 0 | 0.09 | 30.86 | 3.195 | 77.25
95 | -0.82 | 0 | 0.095 | 31.58 | 3.19 | 75.56
100 | -0.82 | 0 | 0.1 | 31.78 | 3.185 | 74.61
105 | -0.83 | 0 | 0.105 | 31.78 | 3.18 | 73.7
110 | -0.83 | 0 | 0.11 | 31.69 | 3.175 | 71.97
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
