bluepylons/Open-Switch-Curve-Meter/Force curves/April-10-21-calibration/Outemu-Silent-Sky-Stem-in-Cherry-MX-Clear-housing.ods

Raw data |  |  | Corrected Downstroke |  | Corrected Upstroke
X (microns) | Force (gf) | Actuated? | X (mm) | Force (gf) | X (mm) | Force (gf)
0 | -0.82 | 0 | 0 | 0.7 | 3.305 | 98.96
5 | -0.84 | 0 | 0.005 | 5.01 | 3.3 | 97.9
10 | -0.82 | 0 | 0.01 | 9.68 | 3.295 | 95.74
15 | -0.82 | 0 | 0.015 | 10.59 | 3.29 | 94.65
20 | -0.83 | 0 | 0.02 | 13.11 | 3.285 | 92.56
25 | -0.85 | 0 | 0.025 | 14.16 | 3.28 | 91.59
30 | -0.82 | 0 | 0.03 | 15.22 | 3.275 | 89.67
35 | -0.82 | 0 | 0.035 | 17.46 | 3.27 | 88.74
40 | -0.88 | 0 | 0.04 | 18.65 | 3.265 | 87.83
45 | -0.84 | 0 | 0.045 | 20.82 | 3.26 | 86.08
50 | -0.8 | 0 | 0.05 | 21.64 | 3.255 | 85.2
55 | -0.81 | 0 | 0.055 | 23.06 | 3.25 | 83.45
60 | -0.76 | 0 | 0.06 | 24.11 | 3.245 | 82.53
65 | -0.82 | 0 | 0.065 | 25.08 | 3.24 | 80.9
70 | -0.83 | 0 | 0.07 | 26.72 | 3.235 | 80.07
75 | -0.82 | 0 | 0.075 | 27.34 | 3.23 | 79.29
80 | -0.82 | 0 | 0.08 | 28.67 | 3.225 | 77.78
85 | -0.84 | 0 | 0.085 | 29.38 | 3.22 | 77.12
90 | -0.83 | 0 | 0.09 | 30.4 | 3.215 | 75.78
95 | -0.83 | 0 | 0.095 | 30.79 | 3.21 | 75.12
100 | -0.84 | 0 | 0.1 | 31.54 | 3.205 | 73.77
105 | -0.83 | 0 | 0.105 | 31.91 | 3.2 | 73.24
110 | -0.85 | 0 | 0.11 | 32.25 | 3.195 | 72.71
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
