bluepylons/Open-Switch-Curve-Meter/Force curves/April-10-21-calibration/Outemu-Silent-Sky-Stem-in-T1.ods

Raw data |  |  | Corrected Downstroke |  | Corrected Upstroke
X (microns) | Force (gf) | Actuated? | X (mm) | Force (gf) | X (mm) | Force (gf)
0 | -0.47 | 0 | 0 | 5.78 | 3.055 | 95.46
5 | -0.47 | 0 | 0.005 | 12.17 | 3.05 | 94.12
10 | -0.48 | 0 | 0.01 | 21.21 | 3.045 | 92.8
15 | -0.46 | 0 | 0.015 | 21.08 | 3.04 | 90.66
20 | -0.47 | 0 | 0.02 | 20.54 | 3.035 | 89.35
25 | -0.49 | 0 | 0.025 | 20.83 | 3.03 | 86.86
30 | -0.49 | 0 | 0.03 | 21.27 | 3.025 | 85.51
35 | -0.49 | 0 | 0.035 | 22.59 | 3.02 | 83.51
40 | -0.46 | 0 | 0.04 | 23.01 | 3.015 | 82.33
45 | -0.47 | 0 | 0.045 | 23.84 | 3.01 | 81.34
50 | -0.46 | 0 | 0.05 | 24.14 | 3.005 | 79.01
55 | -0.44 | 0 | 0.055 | 24.67 | 3 | 78.01
60 | -0.48 | 0 | 0.06 | 25.66 | 2.995 | 75.8
65 | -0.46 | 0 | 0.065 | 26.06 | 2.99 | 74.82
70 | -0.46 | 0 | 0.07 | 26.58 | 2.985 | 72.63
75 | -0.45 | 0 | 0.075 | 27.03 | 2.98 | 71.73
80 | -0.47 | 0 | 0.08 | 27.84 | 2.97499999999999 | 70.73
85 | -0.48 | 0 | 0.085 | 28.05 | 2.96999999999999 | 68.76
90 | -0.45 | 0 | 0.09 | 28.1 | 2.96499999999999 | 67.76
95 | -0.46 | 0 | 0.095 | 29.22 | 2.95999999999999 | 66.38
100 | -0.46 | 0 | 0.1 | 29.65 | 2.95499999999999 | 65.65
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
