bluepylons/Open-Switch-Curve-Meter/Force curves/April-20-21-calibration/AEBoards-Naevy-R1-5.ods

Raw data |  |  |  | Corrected Downstroke |  | Corrected Upstroke
X (microns) | Force (gf) | Actuated? | Tared | X (mm) | Force (gf) | X (mm) | Force (gf)
0 | -0.01 | 0 |  | 0 | 5.32 | 2.89 | 64.44
5 | -0.01 | 0 |  | 0.005 | 12.5 | 2.885 | 57.42
10 | -0.01 | 0 |  | 0.01 | 26.67 | 2.88 | 56.54
15 | 0.01 | 0 |  | 0.015 | 30.23 | 2.875 | 56.49
20 | 0.01 | 0 |  | 0.02 | 33.11 | 2.87 | 56.35
25 | 0.01 | 0 |  | 0.025 | 33.98 | 2.865 | 56.35
30 | -0.03 | 0 |  | 0.03 | 34.44 | 2.86 | 56.22
35 | -0.03 | 0 |  | 0.035 | 34.43 | 2.855 | 56.15
40 | 0.01 | 0 |  | 0.04 | 34.54 | 2.85 | 55.87
45 | 0.01 | 0 |  | 0.045 | 34.73 | 2.845 | 55.71
50 | -0.01 | 0 |  | 0.05 | 34.7 | 2.84 | 55.44
55 | 0.01 | 0 |  | 0.055 | 34.74 | 2.835 | 55.31
60 | 0.01 | 0 |  | 0.06 | 34.8 | 2.83 | 55.04
65 | 0 | 0 |  | 0.065 | 34.93 | 2.825 | 54.96
70 | 0 | 0 |  | 0.07 | 34.9 | 2.82 | 54.84
75 | -0.01 | 0 |  | 0.075 | 34.95 | 2.815 | 54.75
80 | 0.01 | 0 |  | 0.08 | 35.02 | 2.81 | 54.7
85 | 0.02 | 0 |  | 0.085 | 35 | 2.805 | 54.63
90 | 0.01 | 0 |  | 0.09 | 34.97 | 2.8 | 54.58
95 | 0.02 | 0 |  | 0.095 | 35 | 2.795 | 54.46
100 | 0.04 | 0 |  | 0.1 | 35.03 | 2.79 | 54.4
105 | 0.04 | 0 |  | 0.105 | 35.05 | 2.785 | 54.38
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
