bluepylons/Open-Switch-Curve-Meter/Force curves/April-20-21-calibration/blank-template-triangles.ods

Raw data |  |  |  | Corrected Downstroke |  | Corrected Upstroke
X (microns) | Force (gf) | Actuated? | Tared | X (mm) | Force (gf) | X (mm) | Force (gf)
0 | -0.3 | 0 | 0 | 0 | 2.31 | 3.51 | 82.02
5 | -0.3 | 0 | 0 | 0.005 | 8.95 | 3.505 | 76.31
10 | -0.3 | 0 | 0 | 0.01 | 23.94 | 3.5 | 66.4
15 | -0.33 | 0 | -0.03 | 0.015 | 30.29 | 3.495 | 64.2
20 | -0.31 | 0 | -0.01 | 0.02 | 31.93 | 3.49 | 63.26
25 | -0.3 | 0 | 0 | 0.025 | 34.38 | 3.485 | 63.23
30 | -0.29 | 0 | 0.01 | 0.03 | 34.82 | 3.48 | 63.16
35 | -0.32 | 0 | -0.02 | 0.035 | 35.02 | 3.475 | 63.15
40 | -0.31 | 0 | -0.01 | 0.04 | 34.99 | 3.47 | 63.14
45 | -0.33 | 0 | -0.03 | 0.045 | 35.03 | 3.465 | 63.11
50 | -0.32 | 0 | -0.02 | 0.05 | 35.02 | 3.46 | 63.07
55 | -0.3 | 0 | 0 | 0.055 | 35.24 | 3.455 | 63.03
60 | -0.33 | 0 | -0.03 | 0.06 | 35.2 | 3.45 | 63.02
65 | -0.3 | 0 | 0 | 0.065 | 35.21 | 3.445 | 62.95
70 | -0.33 | 0 | -0.03 | 0.07 | 35.18 | 3.44 | 62.93
75 | -0.31 | 0 | -0.01 | 0.075 | 35.35 | 3.435 | 62.9
80 | -0.3 | 0 | 0 | 0.08 | 35.33 | 3.43 | 62.88
85 | -0.32 | 0 | -0.02 | 0.085 | 35.34 | 3.425 | 62.86
90 | -0.34 | 0 | -0.04 | 0.09 | 35.36 | 3.42 | 62.86
95 | -0.32 | 0 | -0.02 | 0.095 | 35.42 | 3.415 | 62.76
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
