bluepylons/Open-Switch-Curve-Meter/Force curves/April-20-21-calibration/Gateron-Aliaz.ods

Raw data |  |  |  | Corrected Downstroke |  | Corrected Upstroke
X (microns) | Force (gf) | Actuated? | Tared | X (mm) | Force (gf) | X (mm) | Force (gf)
0 | 0.46 | 0 | 0 | 0 | 0.23 | 4.065 | 114.75
5 | 0.45 | 0 | -0.01 | 0.005 | 0.62 | 4.06 | 109.41
10 | 0.49 | 0 | 0.03 | 0.01 | 0.85 | 4.055 | 98.43
15 | 0.48 | 0 | 0.02 | 0.015 | 1.53 | 4.05 | 89.48
20 | 0.47 | 0 | 0.01 | 0.02 | 2.31 | 4.045 | 85.1
25 | 0.48 | 0 | 0.02 | 0.025 | 9.09 | 4.04 | 78.74
30 | 0.46 | 0 | 0 | 0.03 | 14.69 | 4.035 | 76.23
35 | 0.45 | 0 | -0.01 | 0.035 | 25.27 | 4.02999999999999 | 73.46
40 | 0.46 | 0 | 0 | 0.04 | 30.04 | 4.02499999999999 | 72.26
45 | 0.49 | 0 | 0.03 | 0.045 | 38.2 | 4.01999999999999 | 70.46
50 | 0.48 | 0 | 0.02 | 0.05 | 41.77 | 4.01499999999999 | 69.8
55 | 0.45 | 0 | -0.01 | 0.055 | 41.76 | 4.00999999999999 | 69.36
60 | 0.46 | 0 | 0 | 0.06 | 41.02 | 4.00499999999999 | 69.25
65 | 0.48 | 0 | 0.02 | 0.065 | 40.92 | 3.99999999999999 | 69.25
70 | 0.49 | 0 | 0.03 | 0.07 | 40.92 | 3.99499999999999 | 69.21
75 | 0.49 | 0 | 0.03 | 0.075 | 40.8 | 3.98999999999999 | 69.13
80 | 0.44 | 0 | -0.02 | 0.08 | 40.74 | 3.98499999999998 | 69.08
85 | 0.46 | 0 | 0 | 0.085 | 40.65 | 3.97999999999998 | 68.97
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
