bluepylons/Open-Switch-Curve-Meter/Force curves/April-20-21-calibration/Gazzew-Boba-U4T.ods

Raw data |  |  |  | Corrected Downstroke |  | Corrected Upstroke
X (microns) | Force (gf) | Actuated? | Tared | X (mm) | Force (gf) | X (mm) | Force (gf)
0 | 0.35 | 0 | -0.01 | 0 | 0.59 | 3.135 | 57.11
5 | 0.33 | 0 | -0.03 | 0.005 | 4.36 | 3.13 | 57.18
10 | 0.34 | 0 | -0.02 | 0.01 | 18.89 | 3.125 | 57.17
15 | 0.36 | 0 | 0 | 0.015 | 27.07 | 3.12 | 57.18
20 | 0.37 | 0 | 0.01 | 0.02 | 37.08 | 3.115 | 57.19
25 | 0.36 | 0 | 0 | 0.025 | 38.74 | 3.11 | 57.17
30 | 0.37 | 0 | 0.01 | 0.03 | 42.05 | 3.105 | 57.17
35 | 0.38 | 0 | 0.02 | 0.035 | 43.38 | 3.1 | 57.13
40 | 0.37 | 0 | 0.01 | 0.04 | 43.49 | 3.095 | 57.12
45 | 0.38 | 0 | 0.02 | 0.045 | 43.29 | 3.09 | 57.1
50 | 0.35 | 0 | -0.01 | 0.05 | 43.51 | 3.085 | 57.1
55 | 0.35 | 0 | -0.01 | 0.055 | 43.78 | 3.08 | 57.09
60 | 0.37 | 0 | 0.01 | 0.06 | 44.01 | 3.075 | 57.02
65 | 0.37 | 0 | 0.01 | 0.065 | 44.05 | 3.07 | 57.01
70 | 0.37 | 0 | 0.01 | 0.07 | 44.21 | 3.065 | 57.06
75 | 0.38 | 0 | 0.02 | 0.075 | 44.55 | 3.06 | 56.99
80 | 0.4 | 0 | 0.04 | 0.08 | 44.82 | 3.055 | 56.95
85 | 0.39 | 0 | 0.03 | 0.085 | 45.2 | 3.05 | 56.91
90 | 0.4 | 0 | 0.04 | 0.09 | 45.43 | 3.045 | 56.89
95 | 0.42 | 0 | 0.06 | 0.095 | 45.88 | 3.04 | 56.87
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
