bluepylons/Open-Switch-Curve-Meter/Force curves/April-20-21-calibration/Gazzew-Phoenix-In-Boba-Housing-With-MX-Clear-Spring.ods

Raw data |  |  |  | Corrected Downstroke |  | Corrected Upstroke
X (microns) | Force (gf) | Actuated? | Tared | X (mm) | Force (gf) | X (mm) | Force (gf)
0 | -0.59 | 0 | -0.02 | 0 | 0.28 | 3.885 | 97.45
5 | -0.58 | 0 | -0.01 | 0.005 | 1.83 | 3.88 | 96.74
10 | -0.56 | 0 | 0.01 | 0.01 | 12.26 | 3.875 | 96.38
15 | -0.56 | 0 | 0.01 | 0.015 | 18.7 | 3.87 | 95.9
20 | -0.55 | 0 | 0.02 | 0.02 | 29.89 | 3.865 | 95.72
25 | -0.55 | 0 | 0.02 | 0.025 | 31.68 | 3.86 | 95.49
30 | -0.56 | 0 | 0.01 | 0.03 | 32.5 | 3.855 | 95.26
35 | -0.58 | 0 | -0.01 | 0.035 | 32.83 | 3.85 | 95.13
40 | -0.54 | 0 | 0.03 | 0.04 | 33.3 | 3.845 | 94.84
45 | -0.57 | 0 | 0 | 0.045 | 33.7 | 3.84 | 94.74
50 | -0.6 | 0 | -0.03 | 0.05 | 34.47 | 3.835 | 94.52
55 | -0.57 | 0 | 0 | 0.055 | 35.32 | 3.83 | 94.43
60 | -0.56 | 0 | 0.01 | 0.06 | 36.18 | 3.825 | 94.27
65 | -0.58 | 0 | -0.01 | 0.065 | 39.46 | 3.82 | 94.21
70 | -0.55 | 0 | 0.02 | 0.07 | 41.25 | 3.815 | 94.06
75 | -0.55 | 0 | 0.02 | 0.075 | 42.62 | 3.81 | 93.99
80 | -0.54 | 0 | 0.03 | 0.08 | 42.54 | 3.805 | 93.78
85 | -0.57 | 0 | 0 | 0.085 | 42.59 | 3.8 | 93.69
90 | -0.58 | 0 | -0.01 | 0.09 | 42.61 | 3.795 | 93.57
95 | -0.57 | 0 | 0 | 0.095 | 42.75 | 3.79 | 93.52
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
