bluepylons/Open-Switch-Curve-Meter/Force curves/April-20-21-calibration/JWK-Pewter.ods

Raw data |  |  |  | Corrected Downstroke |  | Corrected Upstroke
X (microns) | Force (gf) | Actuated? | Tared | X (mm) | Force (gf) | X (mm) | Force (gf)
0 | 0.46 | 0 | 0.01 | 0 | 0.2 | 3.815 | 63.62
5 | 0.45 | 0 | 0 | 0.005 | 1.46 | 3.81 | 63.85
10 | 0.44 | 0 | -0.01 | 0.01 | 11.84 | 3.805 | 60.19
15 | 0.46 | 0 | 0.01 | 0.015 | 25.6 | 3.8 | 57.99
20 | 0.48 | 0 | 0.03 | 0.02 | 28.52 | 3.795 | 52.76
25 | 0.46 | 0 | 0.01 | 0.025 | 30.08 | 3.79 | 50.78
30 | 0.45 | 0 | 0 | 0.03 | 29.77 | 3.785 | 49.96
35 | 0.43 | 0 | -0.02 | 0.035 | 29.18 | 3.78 | 50.04
40 | 0.46 | 0 | 0.01 | 0.04 | 29.54 | 3.775 | 49.87
45 | 0.44 | 0 | -0.01 | 0.045 | 29.57 | 3.77 | 49.86
50 | 0.46 | 0 | 0.01 | 0.05 | 29.54 | 3.765 | 50
55 | 0.46 | 0 | 0.01 | 0.055 | 29.67 | 3.76 | 49.95
60 | 0.44 | 0 | -0.01 | 0.06 | 30.19 | 3.755 | 49.93
65 | 0.46 | 0 | 0.01 | 0.065 | 30.79 | 3.75 | 49.76
70 | 0.43 | 0 | -0.02 | 0.07 | 31.11 | 3.745 | 49.88
75 | 0.46 | 0 | 0.01 | 0.075 | 31.77 | 3.74 | 49.99
80 | 0.45 | 0 | 0 | 0.08 | 32.47 | 3.735 | 49.92
85 | 0.43 | 0 | -0.02 | 0.085 | 32.53 | 3.73 | 50.09
90 | 0.43 | 0 | -0.02 | 0.09 | 32.61 | 3.725 | 49.98
95 | 0.45 | 0 | 0 | 0.095 | 32.65 | 3.72 | 49.74
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
