bluepylons/Open-Switch-Curve-Meter/Force curves/April-20-21-calibration/JWK-Twilight.ods

Raw data |  |  |  | Corrected Downstroke |  | Corrected Upstroke
X (microns) | Force (gf) | Actuated? | Tared | X (mm) | Force (gf) | X (mm) | Force (gf)
0 | 0.1 | 0 | -0.01 | 0 | 8.87 | 3.825 | 75.12
5 | 0.13 | 0 | 0.02 | 0.005 | 15.96 | 3.82 | 73.48
10 | 0.13 | 0 | 0.02 | 0.01 | 24.11 | 3.815 | 69.5
15 | 0.13 | 0 | 0.02 | 0.015 | 25.69 | 3.81 | 66.01
20 | 0.13 | 0 | 0.02 | 0.02 | 26.97 | 3.805 | 65.06
25 | 0.1 | 0 | -0.01 | 0.025 | 27.09 | 3.8 | 64.62
30 | 0.11 | 0 | 0 | 0.03 | 26.98 | 3.795 | 64.62
35 | 0.1 | 0 | -0.01 | 0.035 | 27.1 | 3.79 | 64.53
40 | 0.11 | 0 | 0 | 0.04 | 27.22 | 3.785 | 64.46
45 | 0.14 | 0 | 0.03 | 0.045 | 27.74 | 3.78 | 64.4
50 | 0.12 | 0 | 0.01 | 0.05 | 28.25 | 3.775 | 64.34
55 | 0.12 | 0 | 0.01 | 0.055 | 28.7 | 3.77 | 64.3
60 | 0.14 | 0 | 0.03 | 0.06 | 29.24 | 3.765 | 64.23
65 | 0.11 | 0 | 0 | 0.065 | 30.72 | 3.76 | 64.18
70 | 0.16 | 0 | 0.05 | 0.07 | 31.94 | 3.755 | 64.11
75 | 0.13 | 0 | 0.02 | 0.075 | 33.38 | 3.75 | 64.02
80 | 0.17 | 0 | 0.06 | 0.08 | 33.71 | 3.745 | 63.97
85 | 0.31 | 0 | 0.2 | 0.085 | 33.93 | 3.74 | 63.86
90 | 8.98 | 0 | 8.87 | 0.09 | 34.03 | 3.735 | 63.77
95 | 16.07 | 0 | 15.96 | 0.095 | 34.18 | 3.73 | 63.71
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
