bluepylons/Open-Switch-Curve-Meter/Force curves/April-20-21-calibration/KTT-Matcha.ods

Raw data |  |  |  | Corrected Downstroke |  | Corrected Upstroke
X (microns) | Force (gf) | Actuated? | Tared | X (mm) | Force (gf) | X (mm) | Force (gf)
0 | -0.05 | 0 | 0 | 0 | 9.3 | 3.855 | 56.83
5 | -0.05 | 0 | 0 | 0.005 | 25.53 | 3.85 | 56.85
10 | -0.05 | 0 | 0 | 0.01 | 32.17 | 3.845 | 56.83
15 | -0.04 | 0 | 0.01 | 0.015 | 35.37 | 3.84 | 56.76
20 | -0.08 | 0 | -0.03 | 0.02 | 36.39 | 3.835 | 56.71
25 | -0.08 | 0 | -0.03 | 0.025 | 38.42 | 3.83 | 56.6
30 | -0.06 | 0 | -0.01 | 0.03 | 39.36 | 3.825 | 56.62
35 | -0.09 | 0 | -0.04 | 0.035 | 40.52 | 3.82 | 56.43
40 | -0.06 | 0 | -0.01 | 0.04 | 40.61 | 3.815 | 56.39
45 | -0.05 | 0 | 0 | 0.045 | 40.61 | 3.81 | 56.43
50 | -0.05 | 0 | 0 | 0.05 | 40.73 | 3.805 | 56.45
55 | 0 | 0 | 0.05 | 0.055 | 41.07 | 3.8 | 56.55
60 | -0.05 | 0 | 0 | 0.06 | 41.31 | 3.795 | 56.5
65 | -0.04 | 0 | 0.01 | 0.065 | 41.8 | 3.79 | 56.36
70 | -0.01 | 0 | 0.04 | 0.07 | 42.01 | 3.785 | 56.23
75 | -0.02 | 0 | 0.03 | 0.075 | 42.37 | 3.78 | 56.16
80 | -0.06 | 0 | -0.01 | 0.08 | 42.43 | 3.775 | 56.08
85 | -0.03 | 0 | 0.02 | 0.085 | 42.39 | 3.77 | 56.02
90 | -0.05 | 0 | 0 | 0.09 | 42.5 | 3.765 | 55.94
95 | -0.03 | 0 | 0.02 | 0.095 | 42.49 | 3.76 | 55.91
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
