bluepylons/Open-Switch-Curve-Meter/Force curves/April-4-21-calibration/Gazzew-Boba-U4-68g.png

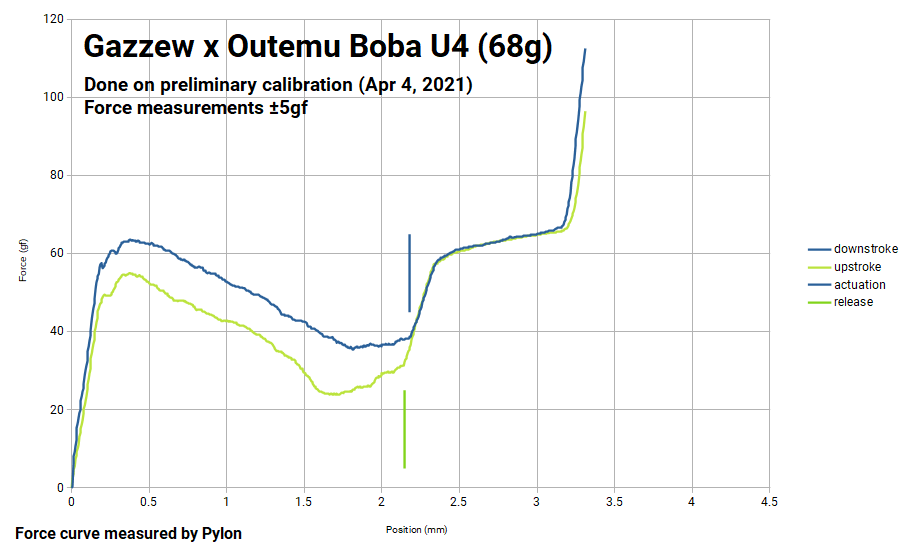
Force curves/April-4-21-calibration/Gazzew-Boba-U4-68g.png
