bluepylons/Open-Switch-Curve-Meter/Force curves/April-4-21-calibration/JWK-Twilight.png

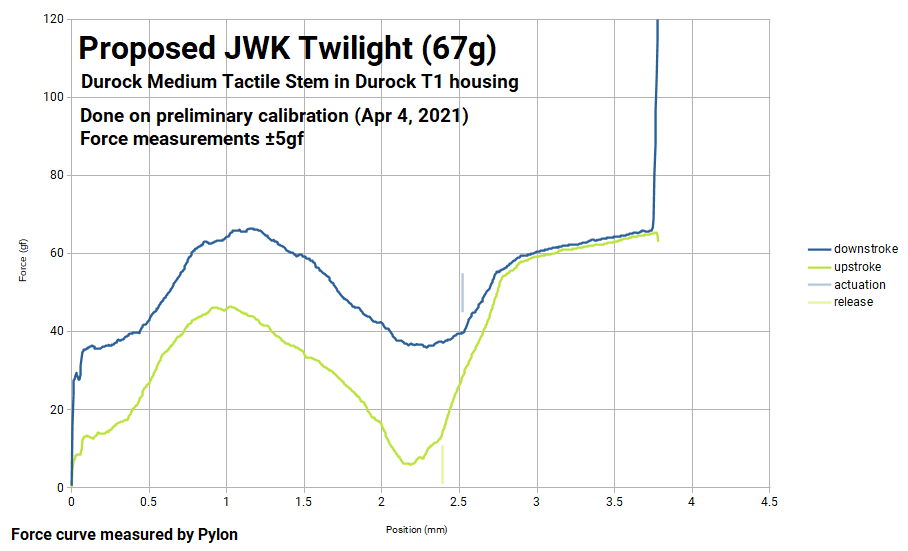
Force curves/April-4-21-calibration/JWK-Twilight.png
