bluepylons/Open-Switch-Curve-Meter/Force curves/April-10-21-calibration/Springs/Sprit-prog-complex-investigation.png

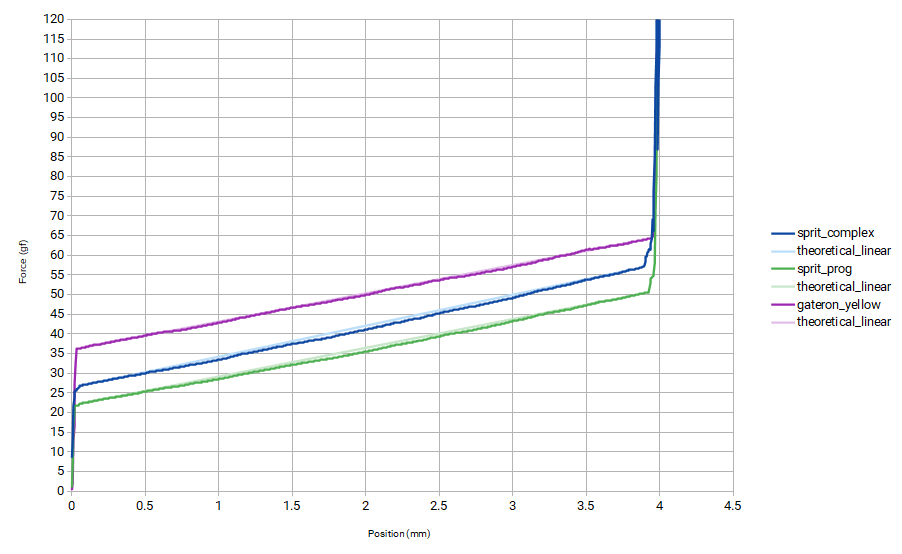
Force curves/April-10-21-calibration/Springs/Sprit-prog-complex-investigation.png
