bluepylons/Open-Switch-Curve-Meter/Force curves/April-20-21-calibration/Zealios-V2-65g.png

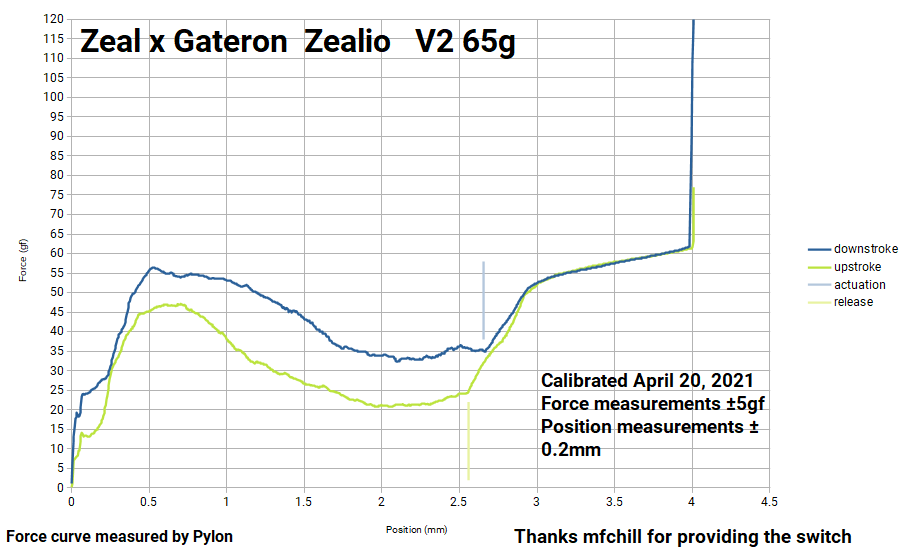
Force curves/April-20-21-calibration/Zealios-V2-65g.png
