bluepylons/Open-Switch-Curve-Meter/Force curves/April-26-21-calibration/Springs/Various-63-5g-springs-redone.png

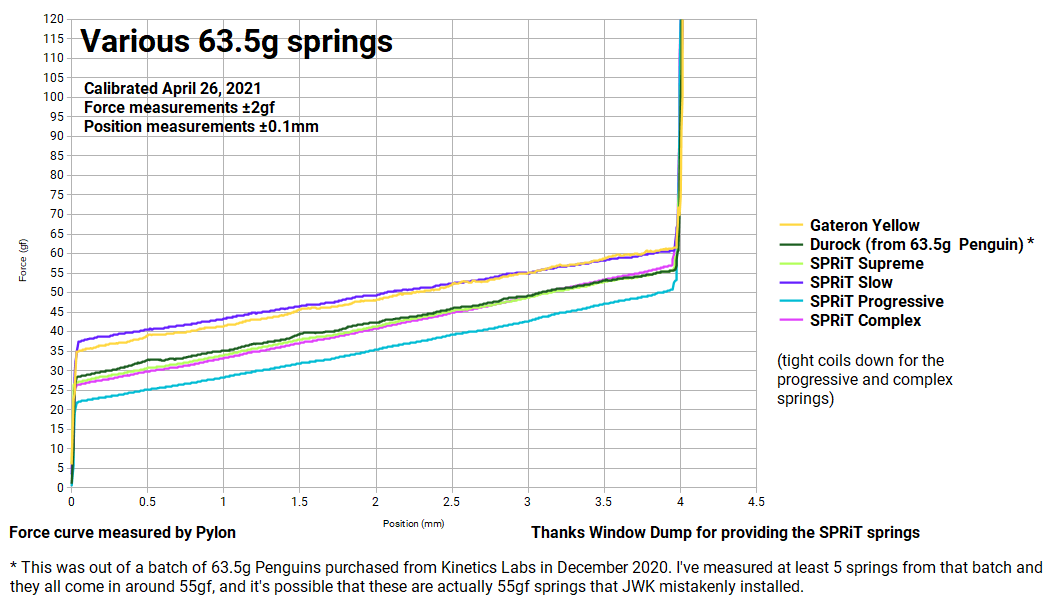
Force curves/April-26-21-calibration/Springs/Various-63-5g-springs-redone.png
