bluepylons/Open-Switch-Curve-Meter/Force curves/Okay-I'm-Just-Going-to-Calibrate-Every-Day-Now/Durock-T1-stem-in-Harimau-housing-T1-comparison.png

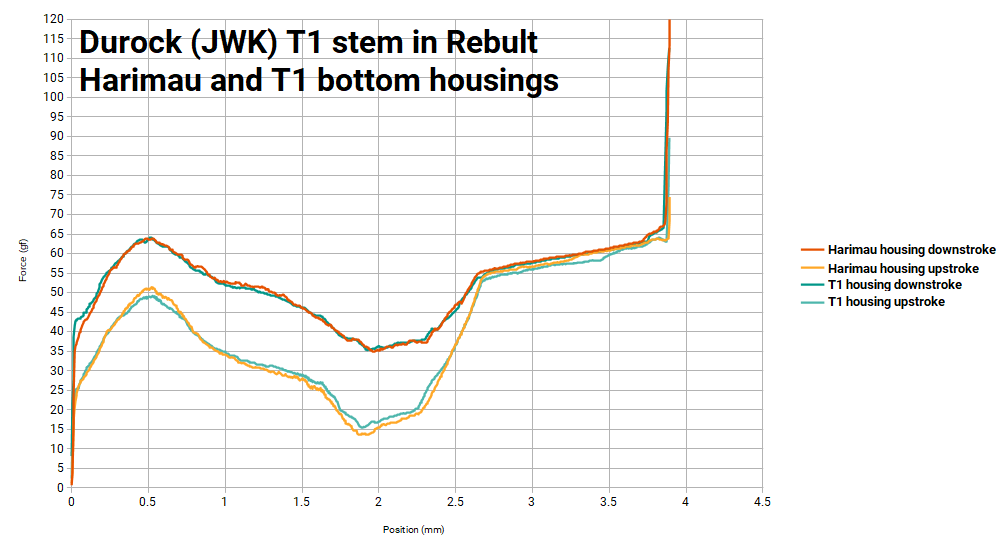
Force curves/Okay-I'm-Just-Going-to-Calibrate-Every-Day-Now/Durock-T1-stem-in-Harimau-housing-T1-comparison.png
