bluepylons/Open-Switch-Curve-Meter/Force curves/Okay-I'm-Just-Going-to-Calibrate-Every-Day-Now/Gazzew-Boba-U4T-stem-in-Halo-Clear.png

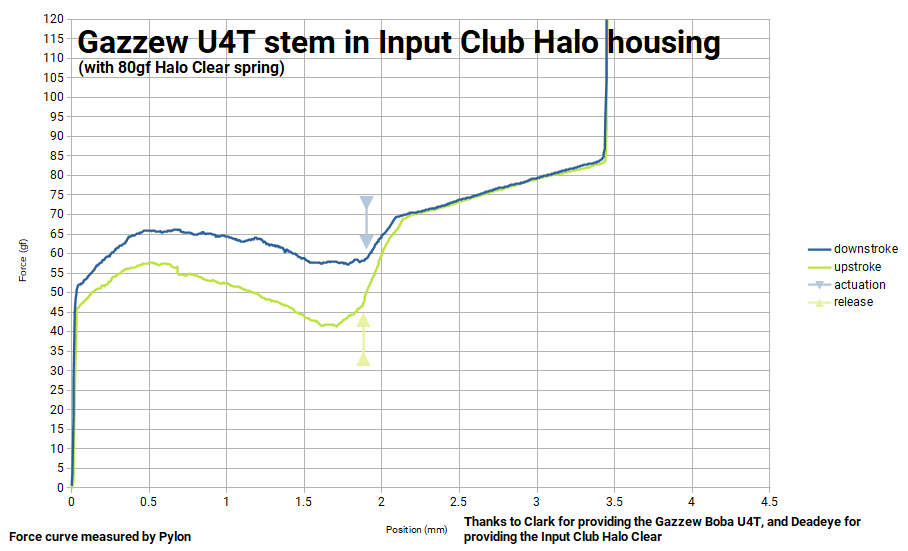
Force curves/Okay-I'm-Just-Going-to-Calibrate-Every-Day-Now/Gazzew-Boba-U4T-stem-in-Halo-Clear.png
