bluepylons/Open-Switch-Curve-Meter/Force curves/Okay-I'm-Just-Going-to-Calibrate-Every-Day-Now/Halo-Stem-Zealio-V2-Bottom-Cherry-Top.png

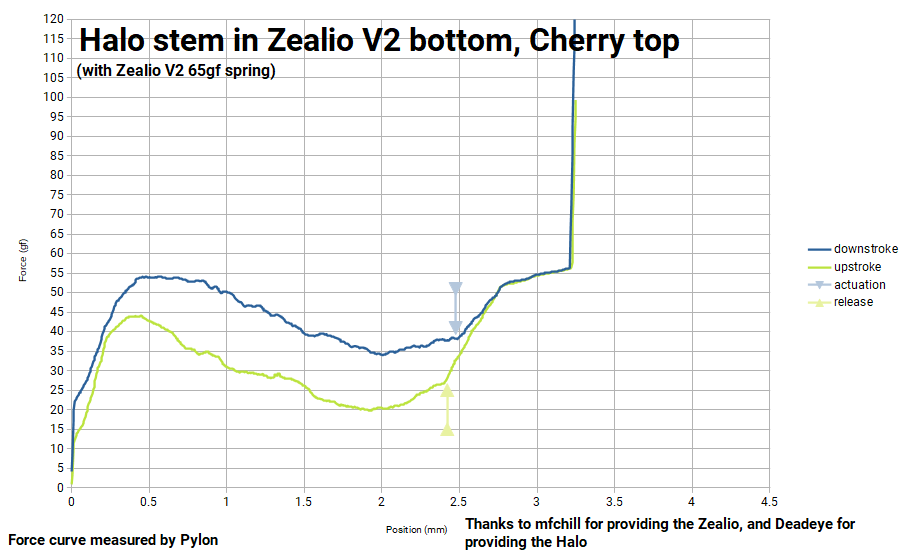
Force curves/Okay-I'm-Just-Going-to-Calibrate-Every-Day-Now/Halo-Stem-Zealio-V2-Bottom-Cherry-Top.png
