bluepylons/Open-Switch-Curve-Meter/Force curves/Okay-I'm-Just-Going-to-Calibrate-Every-Day-Now/Kailh-Box-Crystal-Royal-With-Navy-Clickbar-And-Spring.png

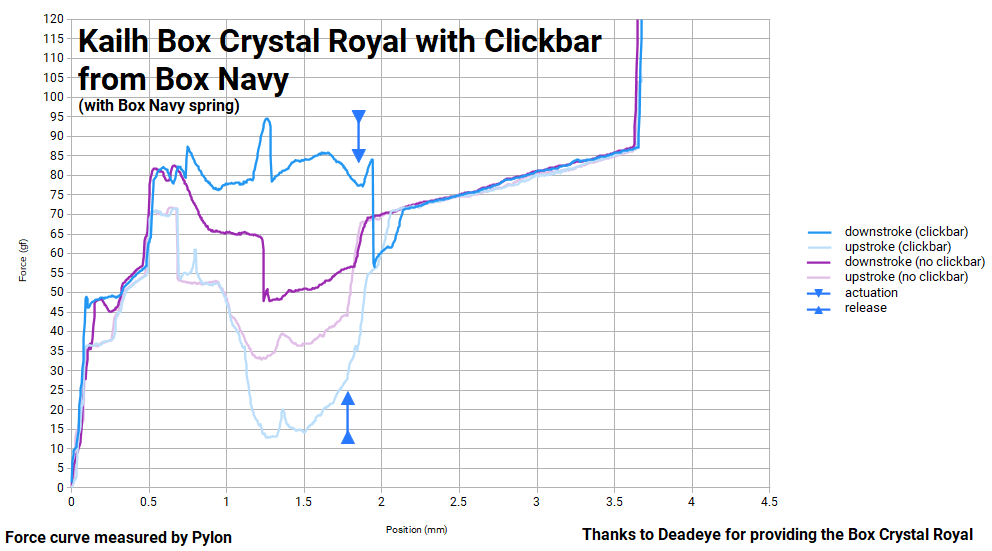
Force curves/Okay-I'm-Just-Going-to-Calibrate-Every-Day-Now/Kailh-Box-Crystal-Royal-With-Navy-Clickbar-And-Spring.png
