bluepylons/Open-Switch-Curve-Meter/Force curves/Okay-I'm-Just-Going-to-Calibrate-Every-Day-Now/NK-Blueberry-stem-in-Boba.png

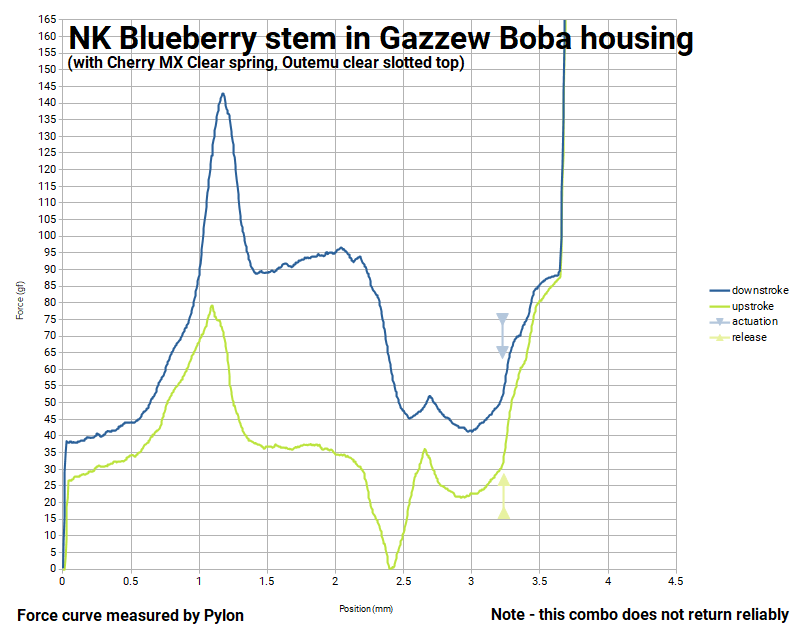
Force curves/Okay-I'm-Just-Going-to-Calibrate-Every-Day-Now/NK-Blueberry-stem-in-Boba.png
