bluepylons/Open-Switch-Curve-Meter/Firmware/Raw-ADC-test/sketch_may11a/sketch_may11a.ino

//We're going to use the G-code M355 to turn the light on and off. 
//The Marlin documentation for M355 is here:
//https://marlinfw.org/docs/gcode/M355.html


#define Channel_1_Pin 2
#define Channel_2_Pin 3
#define Channel_3_Pin 4
#define Channel_4_Pin 5

void setup() {
  // put your setup code here, to run once:

}

void loop() {
  // put your main code here, to run repeatedly:

}
